Electrium-Mobility/Bakfiets-F26/docs/images/cad-previews/3_hole_connecting_part.png

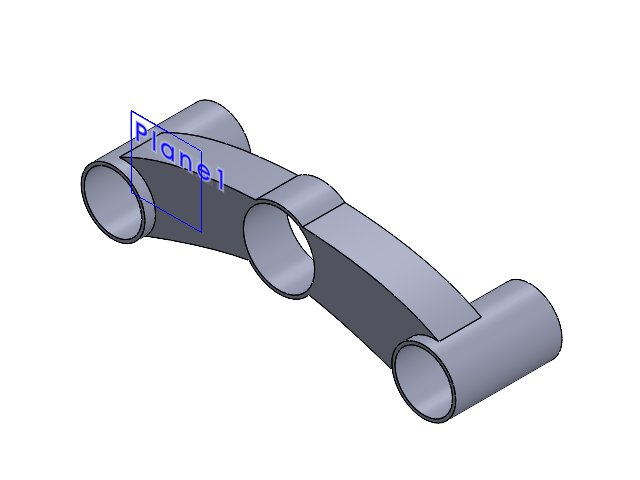
docs/images/cad-previews/3_hole_connecting_part.png
