Electrium-Mobility/Bakfiets-F26/docs/images/cad-previews/91280A626_Medium_Strength_Class_8_8_Steel_Hex_Head_Screw.png

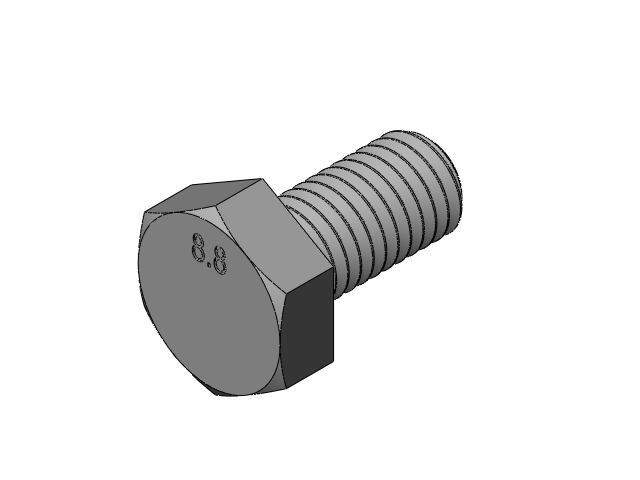
docs/images/cad-previews/91280A626_Medium_Strength_Class_8_8_Steel_Hex_Head_Screw.png
