Electrium-Mobility/Bakfiets-F26/docs/images/cad-previews/Aluminum_Angle_1_25_x_0_125_.png

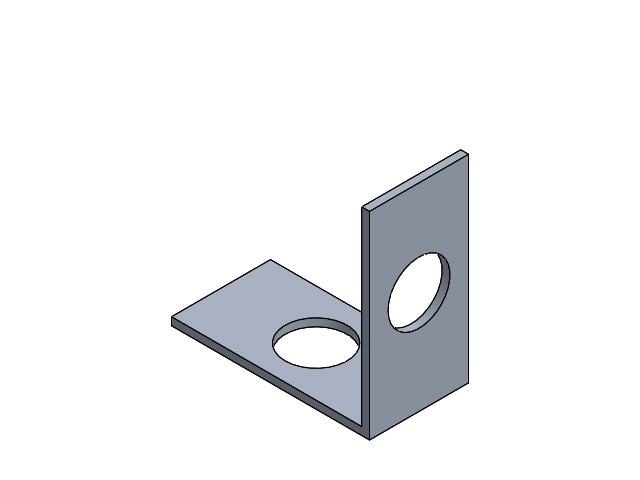
docs/images/cad-previews/Aluminum_Angle_1_25_x_0_125_.png
