Electrium-Mobility/Bakfiets-F26/docs/images/cad-previews/Antispark.png

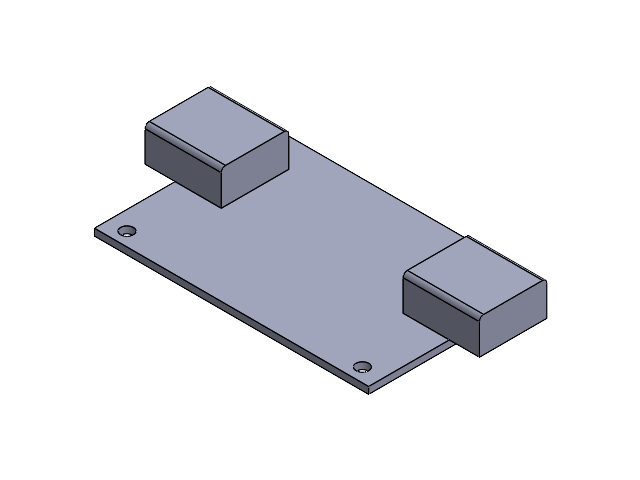
docs/images/cad-previews/Antispark.png
