Electrium-Mobility/Bakfiets-F26/docs/images/cad-previews/Assem1.png

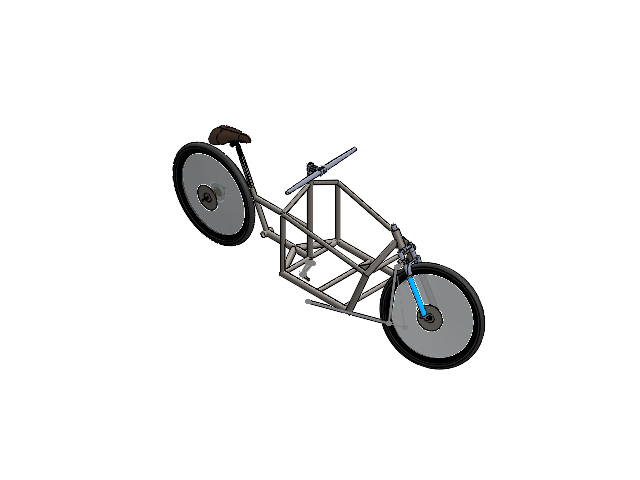
docs/images/cad-previews/Assem1.png
