Electrium-Mobility/Bakfiets-F26/docs/images/cad-previews/bakfiets_front_fork.png

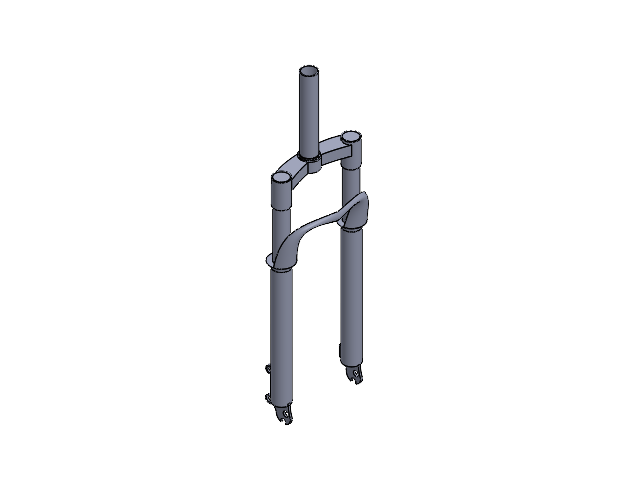
docs/images/cad-previews/bakfiets_front_fork.png
