Electrium-Mobility/Bakfiets-F26/docs/images/cad-previews/ball.png

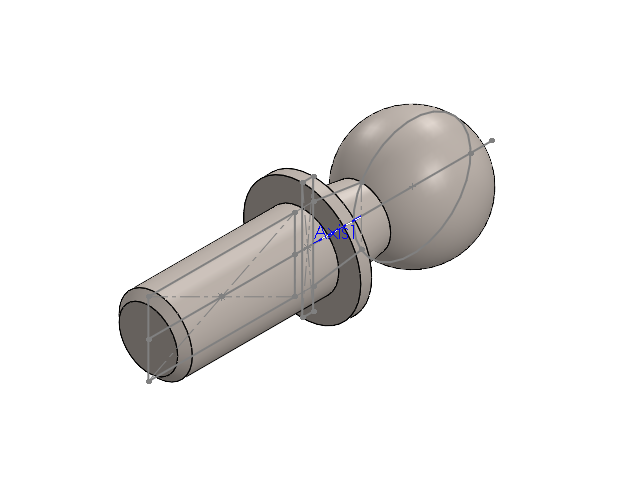
docs/images/cad-previews/ball.png
