Electrium-Mobility/Bakfiets-F26/docs/images/cad-previews/ball_joint.png

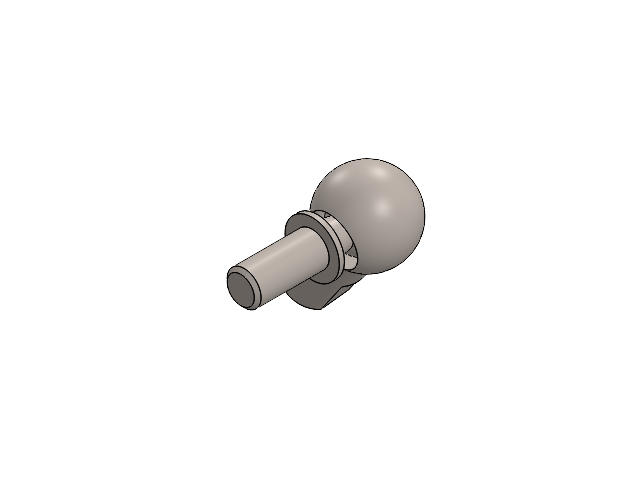
docs/images/cad-previews/ball_joint.png
