Electrium-Mobility/Bakfiets-F26/docs/images/cad-previews/BottomBracketClamp.png

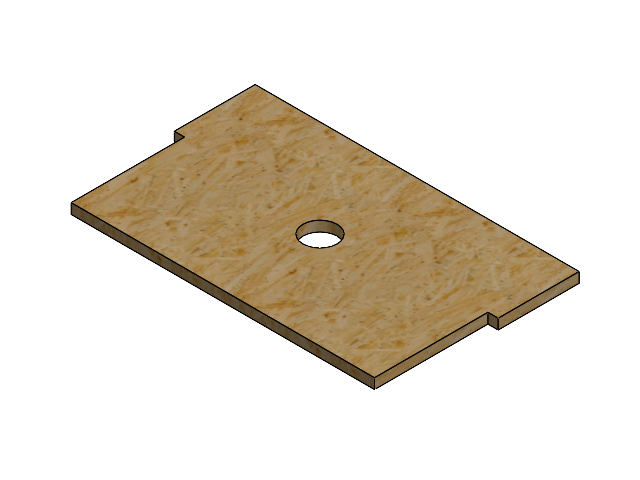
docs/images/cad-previews/BottomBracketClamp.png
