Electrium-Mobility/Bakfiets-F26/docs/images/cad-previews/BottomBracketSupport.png

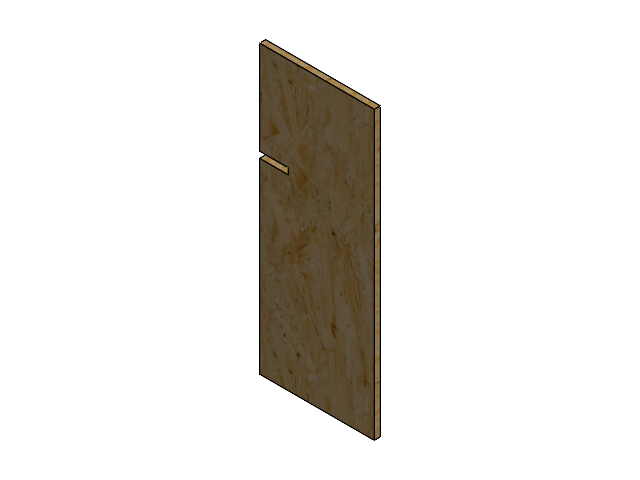
docs/images/cad-previews/BottomBracketSupport.png
