Electrium-Mobility/Bakfiets-F26/docs/images/cad-previews/Box_and_Frame.png

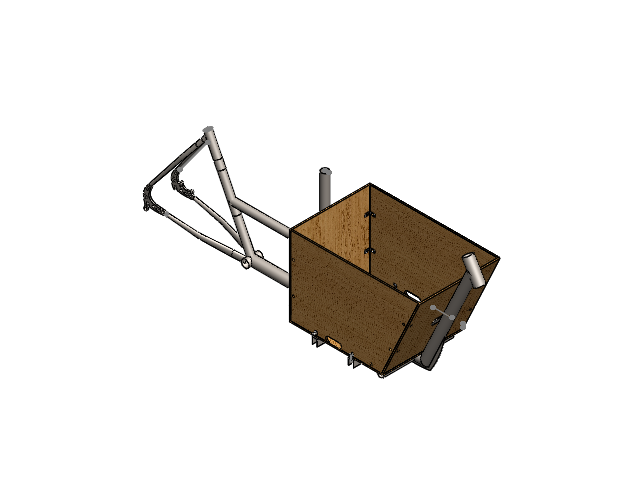
docs/images/cad-previews/Box_and_Frame.png
