Electrium-Mobility/Bakfiets-F26/docs/images/cad-previews/Box_with_angles.png

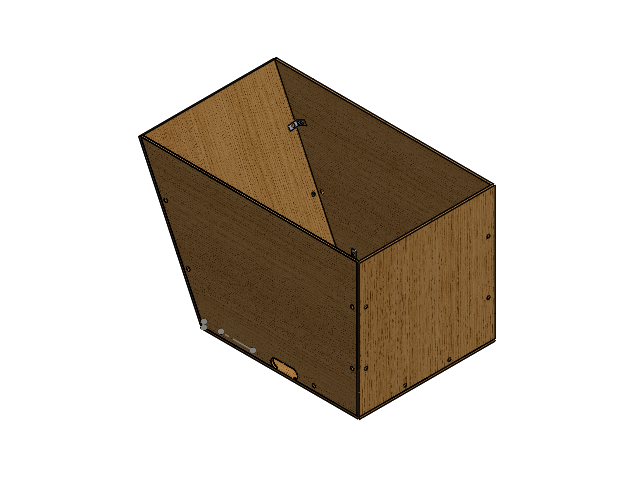
docs/images/cad-previews/Box_with_angles.png
