Electrium-Mobility/Bakfiets-F26/docs/images/cad-previews/Cargo_Box.png

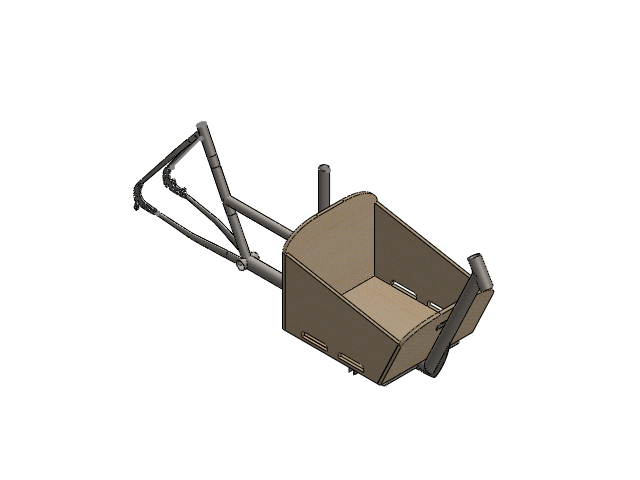
docs/images/cad-previews/Cargo_Box.png
