Electrium-Mobility/Bakfiets-F26/docs/images/cad-previews/Cargo_Box_2.png

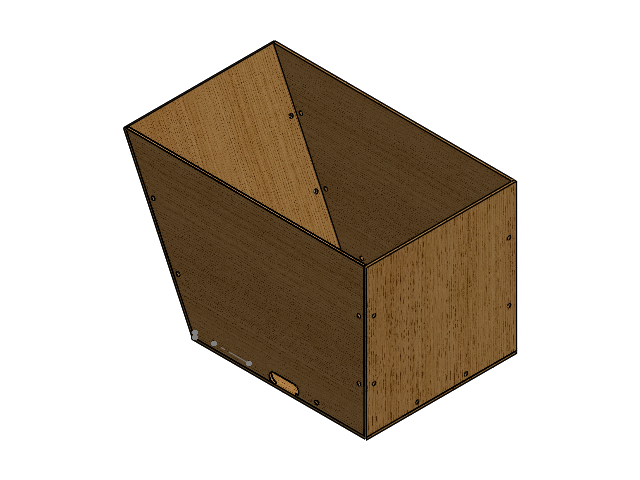
docs/images/cad-previews/Cargo_Box_2.png
