Electrium-Mobility/Bakfiets-F26/docs/images/cad-previews/ChainStaySupport1.png

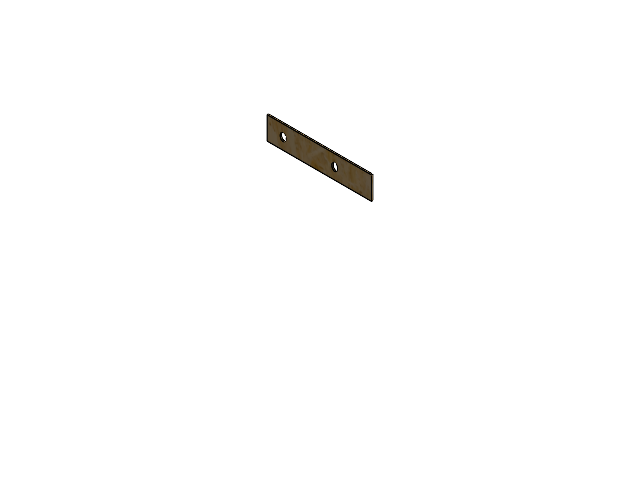
docs/images/cad-previews/ChainStaySupport1.png
