Electrium-Mobility/Bakfiets-F26/docs/images/cad-previews/ChainStaySupport2.png

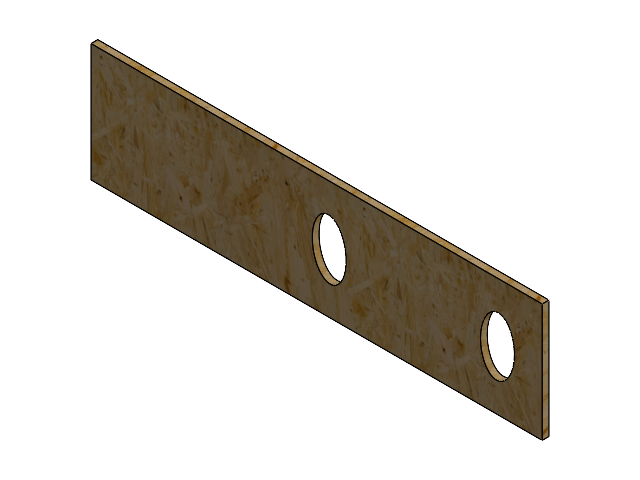
docs/images/cad-previews/ChainStaySupport2.png
