Electrium-Mobility/Bakfiets-F26/docs/images/cad-previews/clamp.png

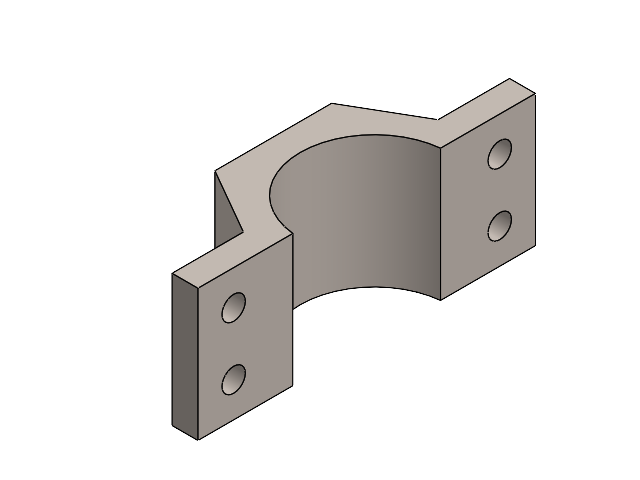
docs/images/cad-previews/clamp.png
