Electrium-Mobility/Bakfiets-F26/docs/images/cad-previews/ConeSupportConnector.png

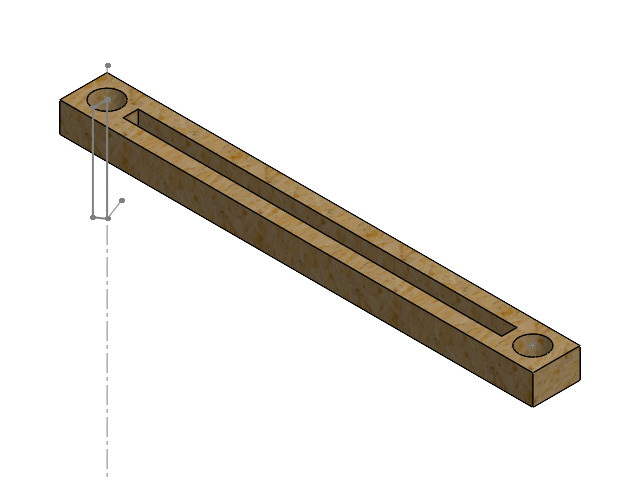
docs/images/cad-previews/ConeSupportConnector.png
