Electrium-Mobility/Bakfiets-F26/docs/images/cad-previews/coop_bakfiets_ball_joint.png

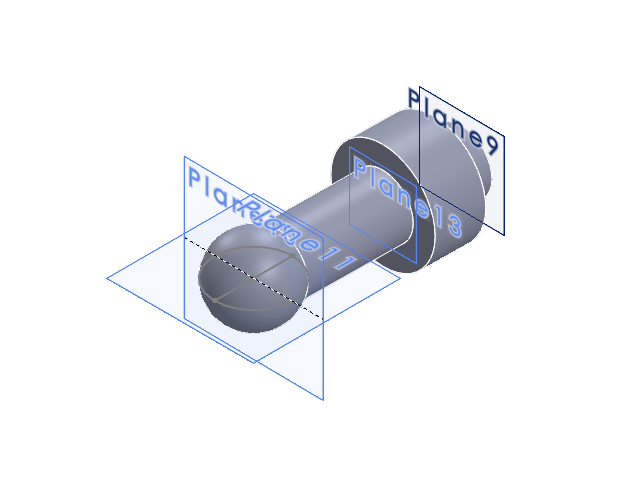
docs/images/cad-previews/coop_bakfiets_ball_joint.png
