Electrium-Mobility/Bakfiets-F26/docs/images/cad-previews/coop_bakfiets_cargo_box_low_detail.png

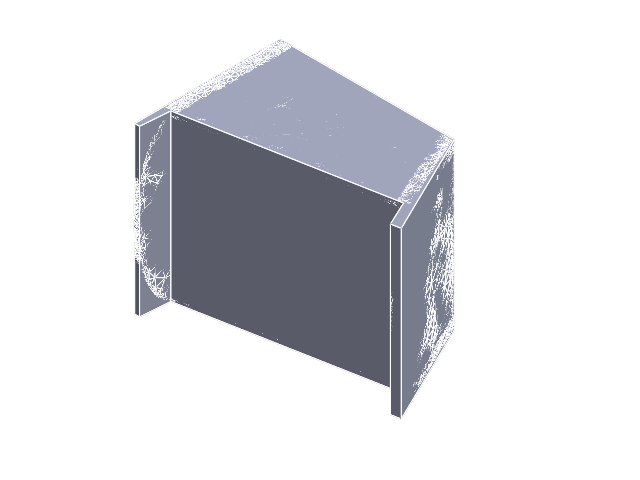
docs/images/cad-previews/coop_bakfiets_cargo_box_low_detail.png
