Electrium-Mobility/Bakfiets-F26/docs/images/cad-previews/coop_bakfiets_frame.png

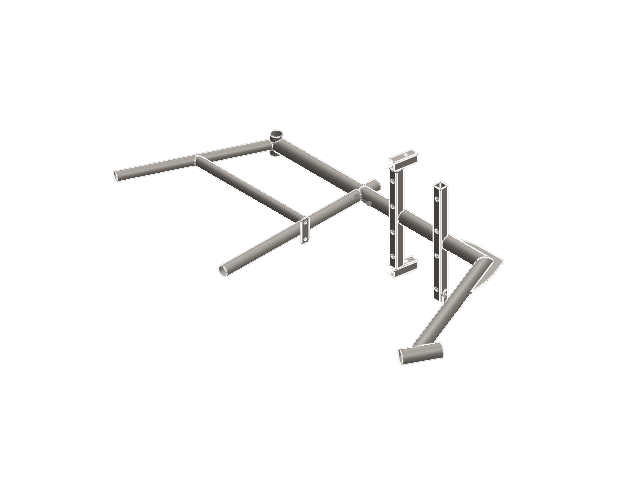
docs/images/cad-previews/coop_bakfiets_frame.png
