Electrium-Mobility/Bakfiets-F26/docs/images/cad-previews/coop_bakfiets_front_suspension.png

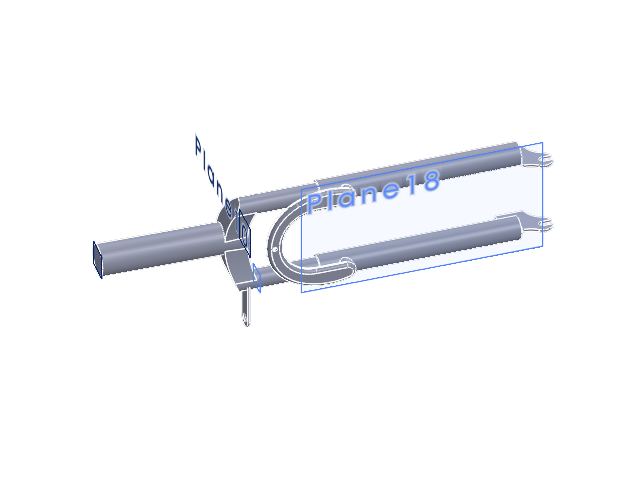
docs/images/cad-previews/coop_bakfiets_front_suspension.png
