Electrium-Mobility/Bakfiets-F26/docs/images/cad-previews/coop_bakfiets_front_wheel.png

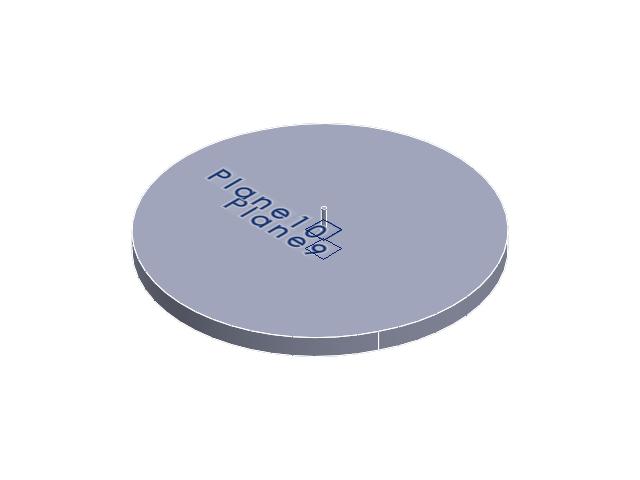
docs/images/cad-previews/coop_bakfiets_front_wheel.png
