Electrium-Mobility/Bakfiets-F26/docs/images/cad-previews/coop_bakfiets_kickstand.png

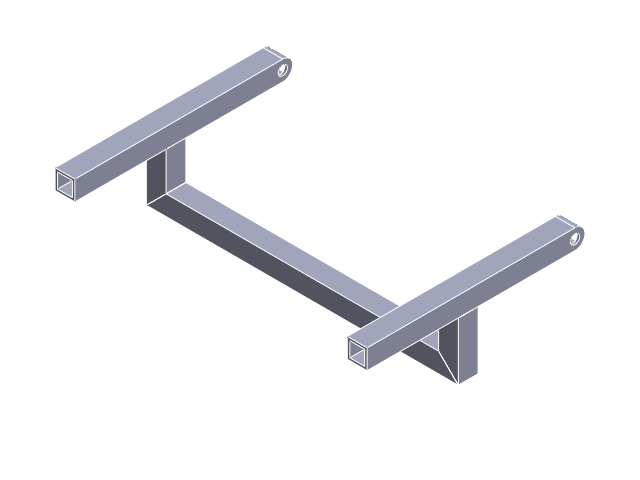
docs/images/cad-previews/coop_bakfiets_kickstand.png
