Electrium-Mobility/Bakfiets-F26/docs/images/cad-previews/coop_bakfiets_main_asm.png

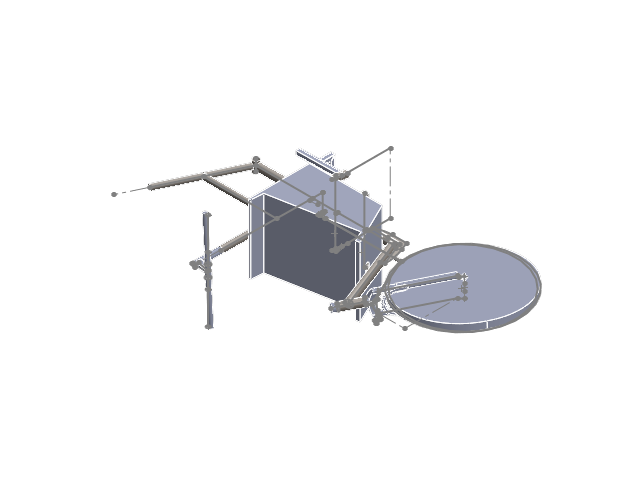
docs/images/cad-previews/coop_bakfiets_main_asm.png
