Electrium-Mobility/Bakfiets-F26/docs/images/cad-previews/coop_bakfiets_master_sketch.png

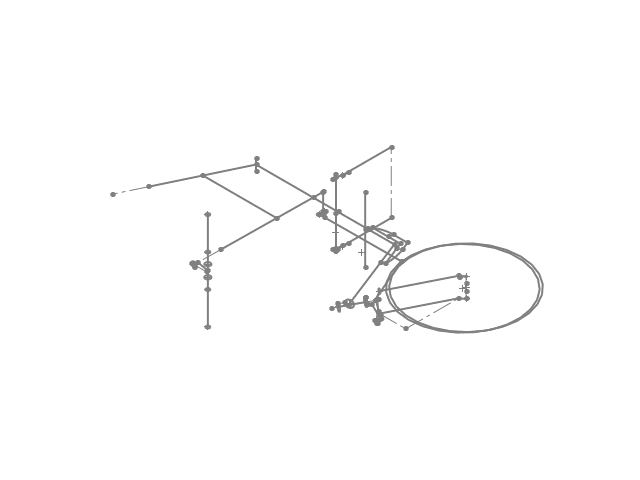
docs/images/cad-previews/coop_bakfiets_master_sketch.png
