Electrium-Mobility/Bakfiets-F26/docs/images/cad-previews/coop_bakfiets_steering_rod.png

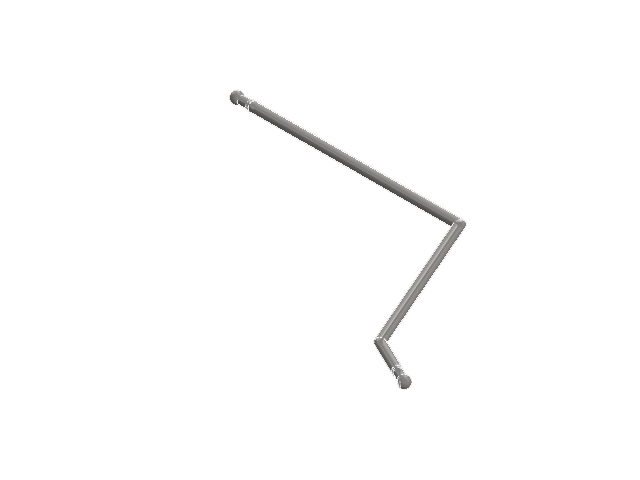
docs/images/cad-previews/coop_bakfiets_steering_rod.png
