Electrium-Mobility/Bakfiets-F26/docs/images/cad-previews/Crank_.png

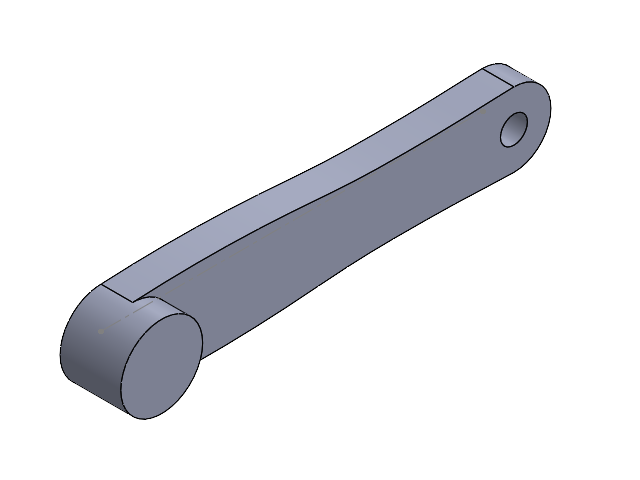
docs/images/cad-previews/Crank_.png
