Electrium-Mobility/Bakfiets-F26/docs/images/cad-previews/Crank_Shaft.png

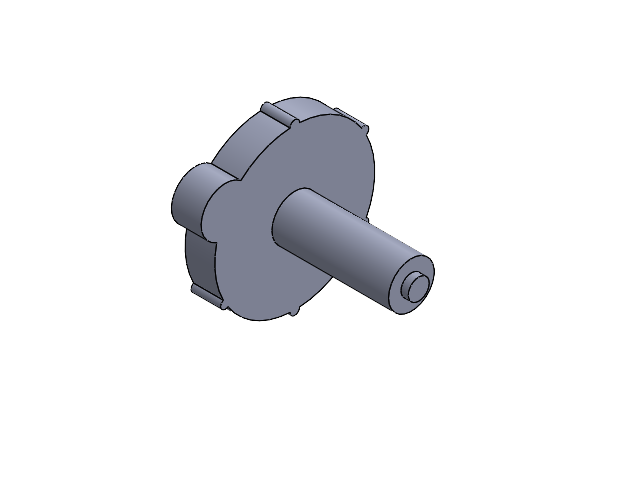
docs/images/cad-previews/Crank_Shaft.png
