Electrium-Mobility/Bakfiets-F26/docs/images/cad-previews/Crank_Wheel.png

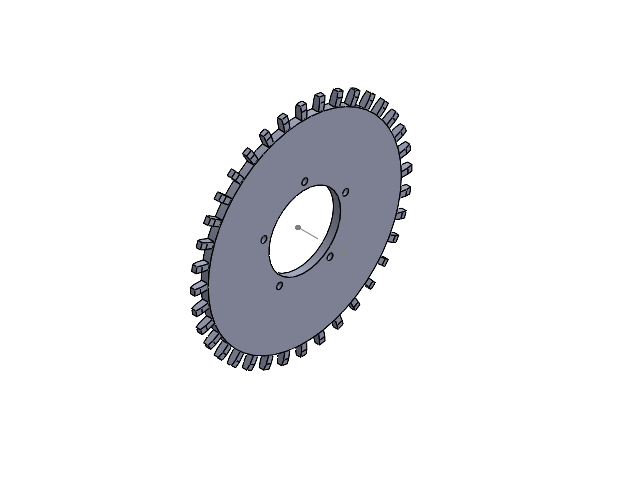
docs/images/cad-previews/Crank_Wheel.png
