Electrium-Mobility/Bakfiets-F26/docs/images/cad-previews/Crank_Wheel_screws.png

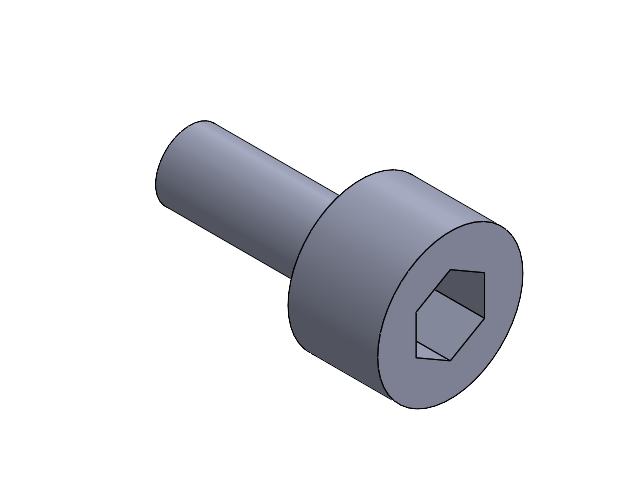
docs/images/cad-previews/Crank_Wheel_screws.png
