Electrium-Mobility/Bakfiets-F26/docs/images/cad-previews/Custom_Angle_for_Sides_3.png

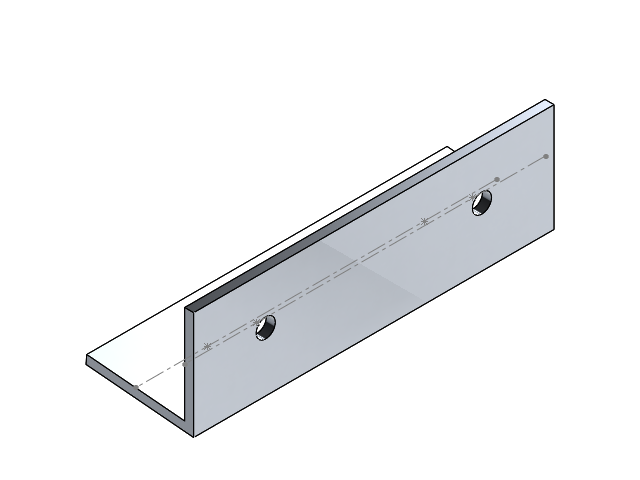
docs/images/cad-previews/Custom_Angle_for_Sides_3.png
