Electrium-Mobility/Bakfiets-F26/docs/images/cad-previews/End1.png

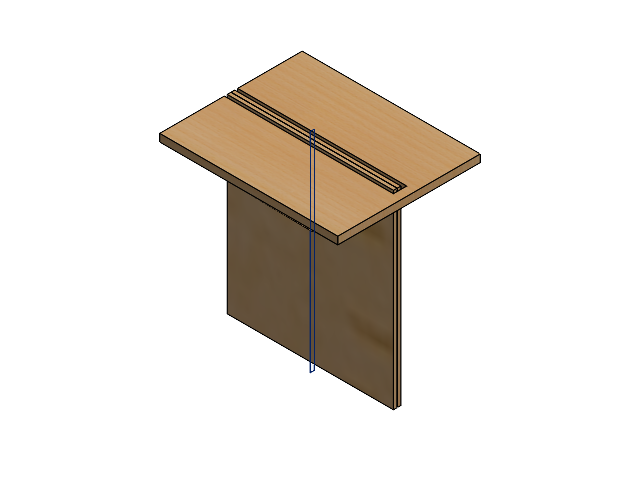
docs/images/cad-previews/End1.png
