Electrium-Mobility/Bakfiets-F26/docs/images/cad-previews/Frame.png

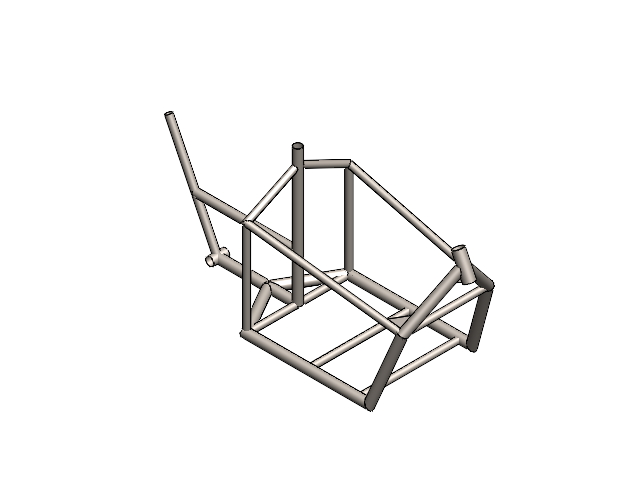
docs/images/cad-previews/Frame.png
