Electrium-Mobility/Bakfiets-F26/docs/images/cad-previews/Frame_2_0.png

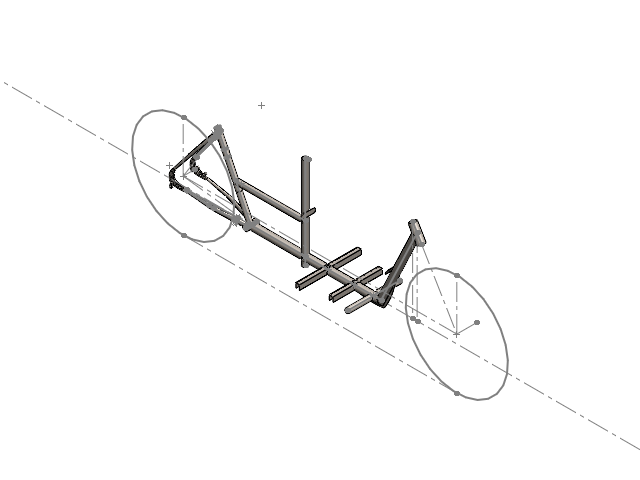
docs/images/cad-previews/Frame_2_0.png
