Electrium-Mobility/Bakfiets-F26/docs/images/cad-previews/Frame_2_0_Sweep8.png

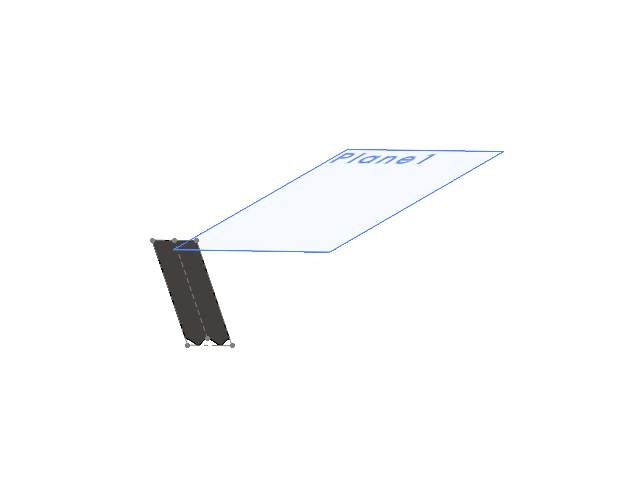
docs/images/cad-previews/Frame_2_0_Sweep8.png
