Electrium-Mobility/Bakfiets-F26/docs/images/cad-previews/front_fork.png

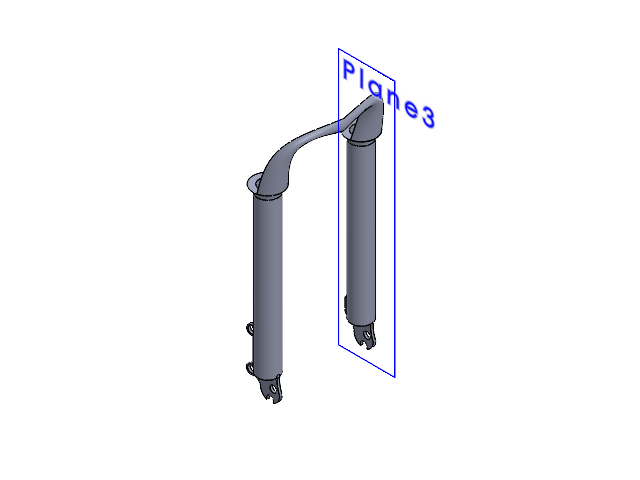
docs/images/cad-previews/front_fork.png
