Electrium-Mobility/Bakfiets-F26/docs/images/cad-previews/front_steering_plate.png

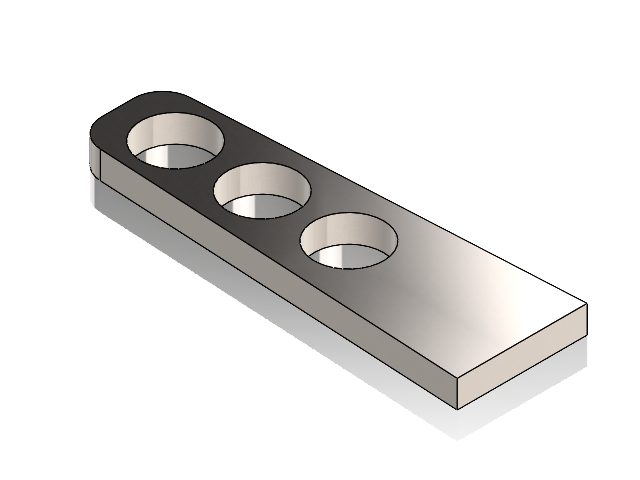
docs/images/cad-previews/front_steering_plate.png
