Electrium-Mobility/Bakfiets-F26/docs/images/cad-previews/front_wheel.png

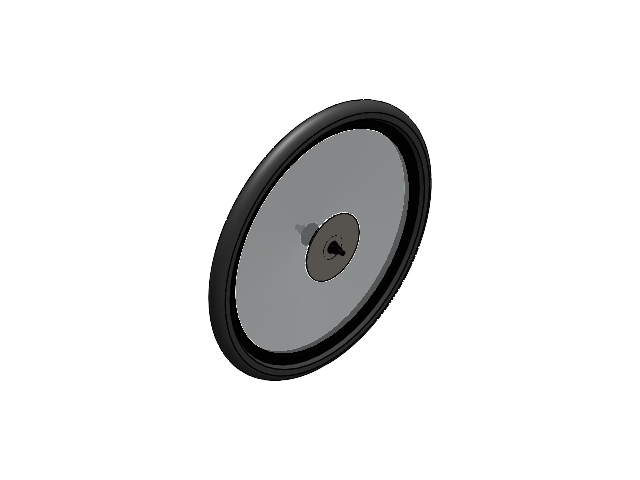
docs/images/cad-previews/front_wheel.png
