Electrium-Mobility/Bakfiets-F26/docs/images/cad-previews/Gusset.png

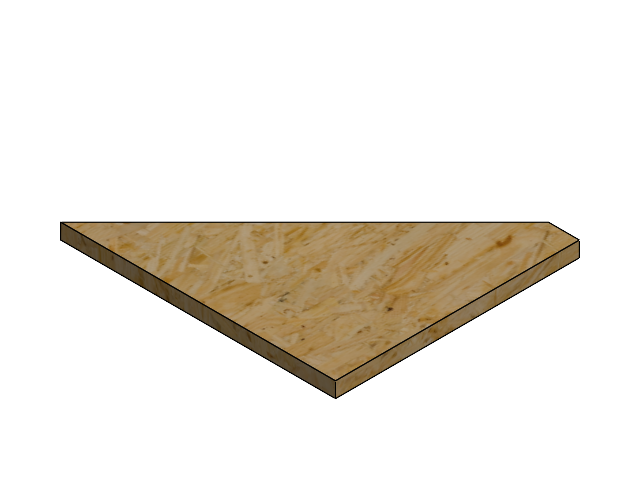
docs/images/cad-previews/Gusset.png
