Electrium-Mobility/Bakfiets-F26/docs/images/cad-previews/handlebar_stem.png

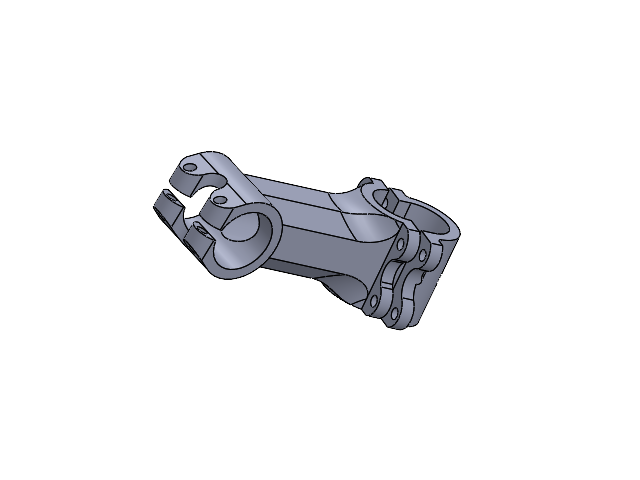
docs/images/cad-previews/handlebar_stem.png
