Electrium-Mobility/Bakfiets-F26/docs/images/cad-previews/handlebars_rod.png

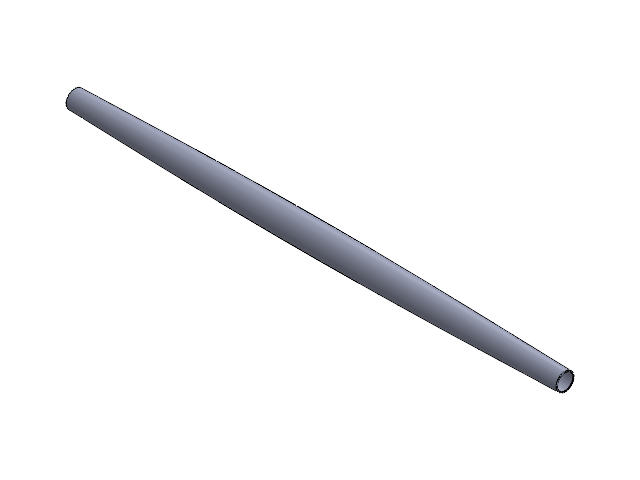
docs/images/cad-previews/handlebars_rod.png
