Electrium-Mobility/Bakfiets-F26/docs/images/cad-previews/JigBaseMDFNew1.png

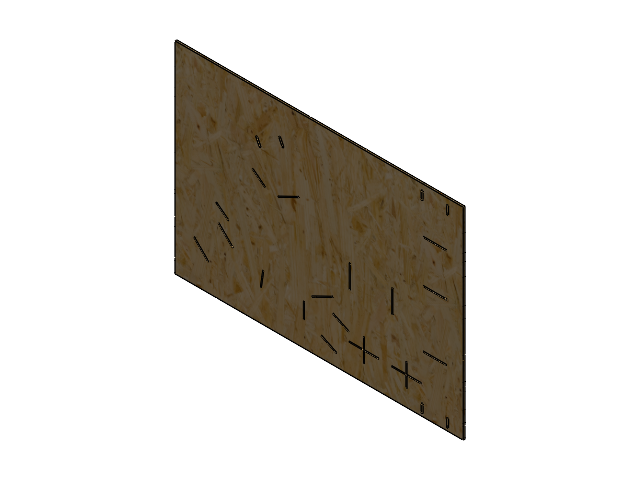
docs/images/cad-previews/JigBaseMDFNew1.png
