Electrium-Mobility/Bakfiets-F26/docs/images/cad-previews/JigCone.png

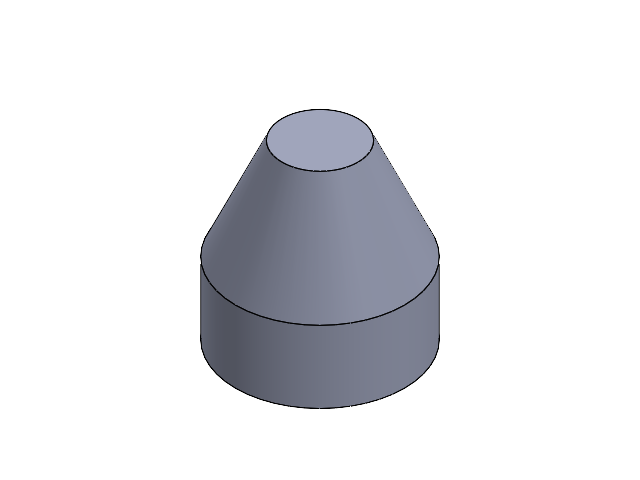
docs/images/cad-previews/JigCone.png
