Electrium-Mobility/Bakfiets-F26/docs/images/cad-previews/JigV2.png

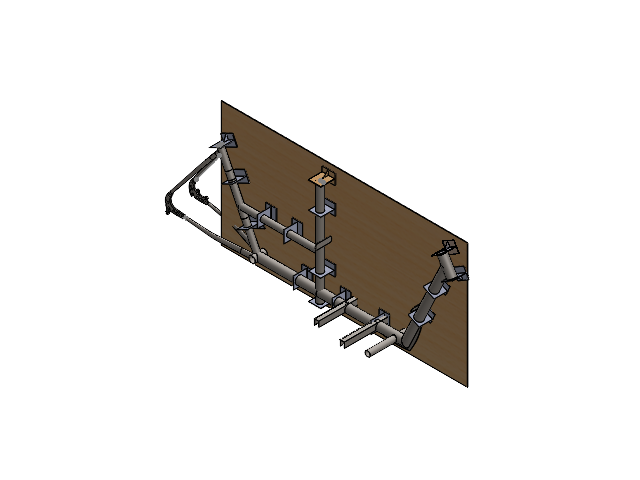
docs/images/cad-previews/JigV2.png
