Electrium-Mobility/Bakfiets-F26/docs/images/cad-previews/Kickstand.png

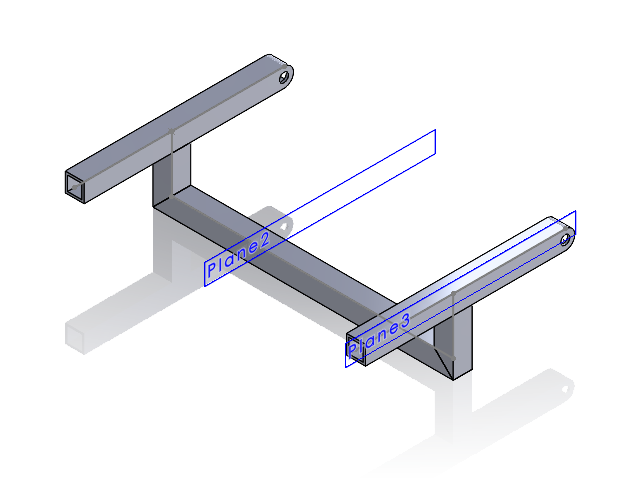
docs/images/cad-previews/Kickstand.png
