Electrium-Mobility/Bakfiets-F26/docs/images/cad-previews/KickstandBracketFeb15.png

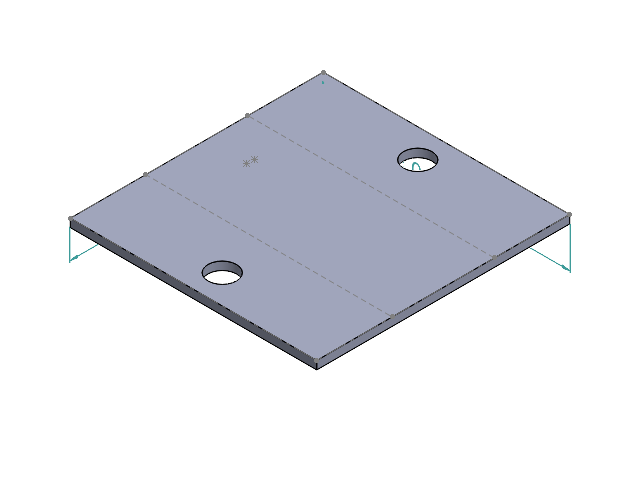
docs/images/cad-previews/KickstandBracketFeb15.png
