Electrium-Mobility/Bakfiets-F26/docs/images/cad-previews/Main_Tube_to_BB.png

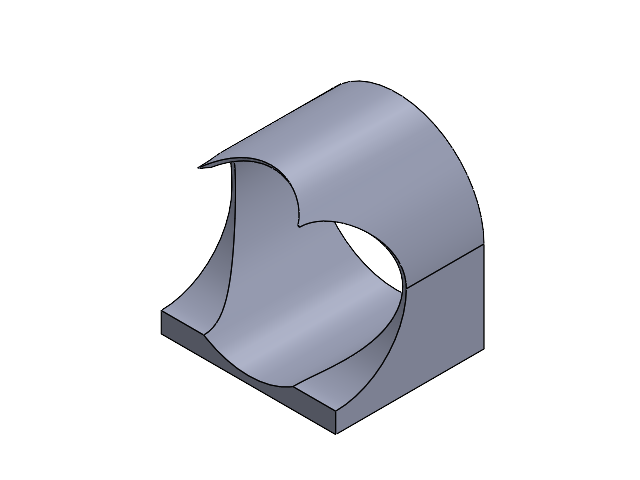
docs/images/cad-previews/Main_Tube_to_BB.png
