Electrium-Mobility/Bakfiets-F26/docs/images/cad-previews/Main_Tube_to_MTH.png

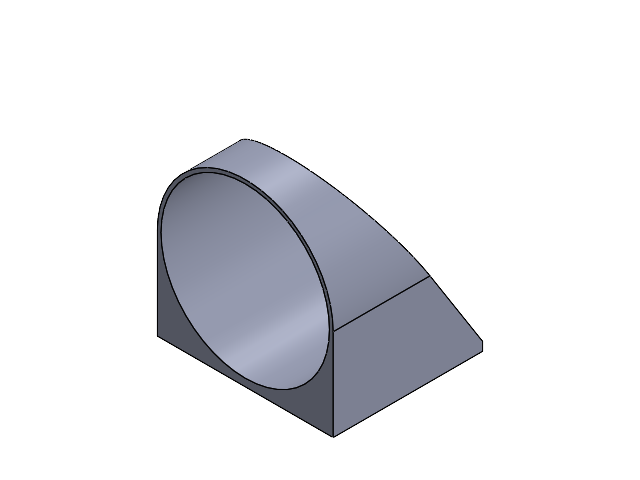
docs/images/cad-previews/Main_Tube_to_MTH.png
