Electrium-Mobility/Bakfiets-F26/docs/images/cad-previews/Motor.png

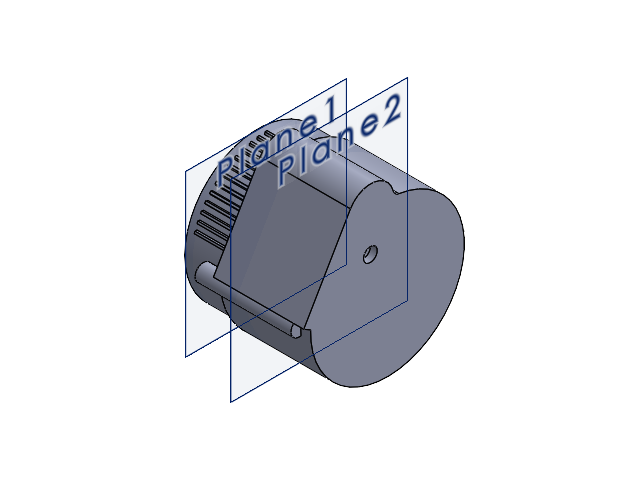
docs/images/cad-previews/Motor.png
