Electrium-Mobility/Bakfiets-F26/docs/images/cad-previews/rear_steering_plate.png

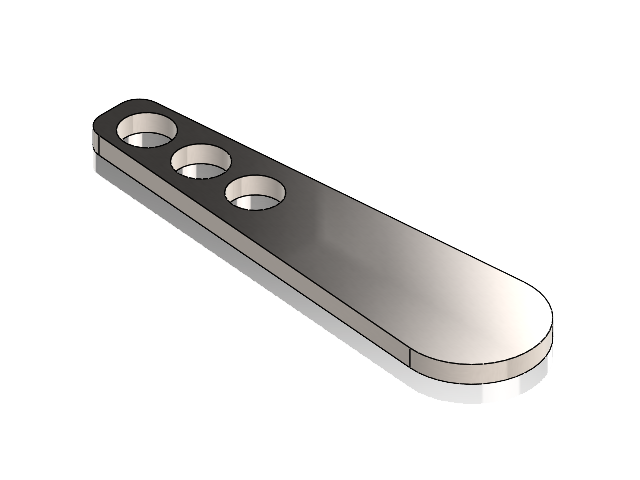
docs/images/cad-previews/rear_steering_plate.png
