Electrium-Mobility/Bakfiets-F26/docs/images/cad-previews/seat.png

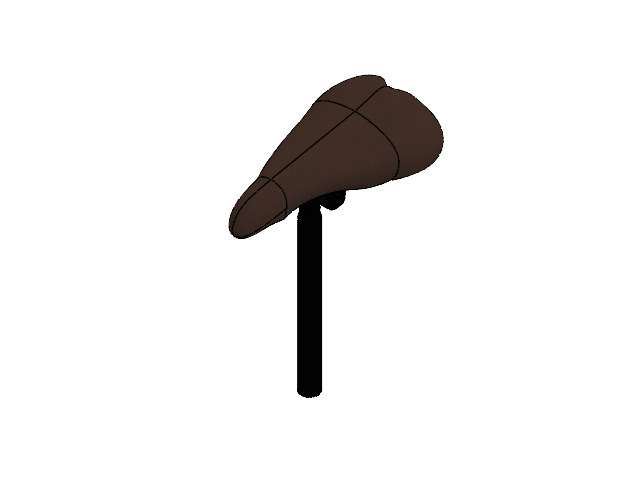
docs/images/cad-previews/seat.png
