Electrium-Mobility/Bakfiets-F26/docs/images/cad-previews/Seat_tube_430_mm_.png

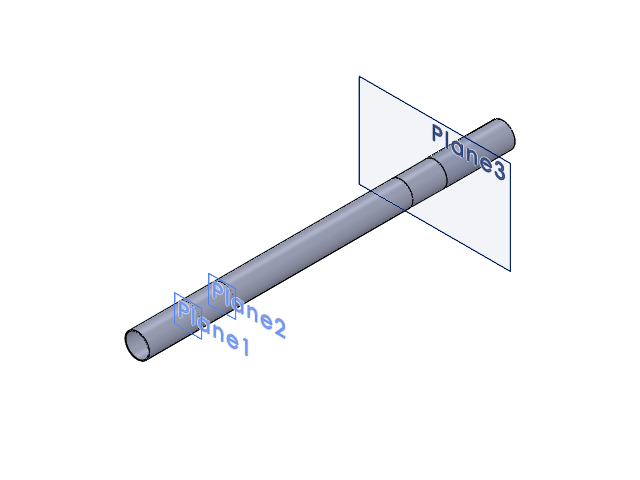
docs/images/cad-previews/Seat_tube_430_mm_.png
