Electrium-Mobility/Bakfiets-F26/docs/images/cad-previews/steering_shaft.png

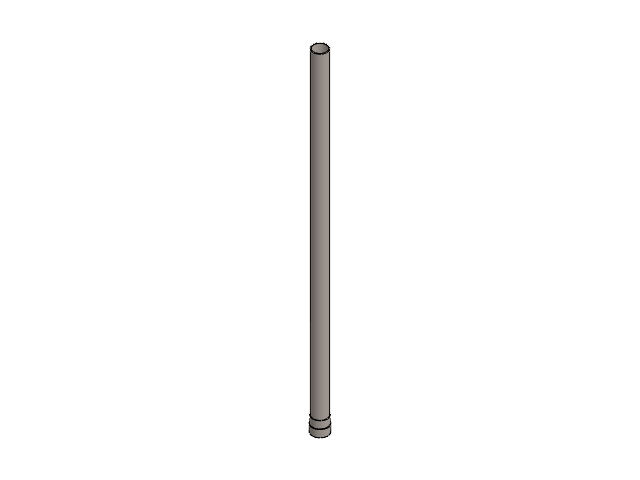
docs/images/cad-previews/steering_shaft.png
