Electrium-Mobility/Bakfiets-F26/docs/images/cad-previews/steeringLink.png

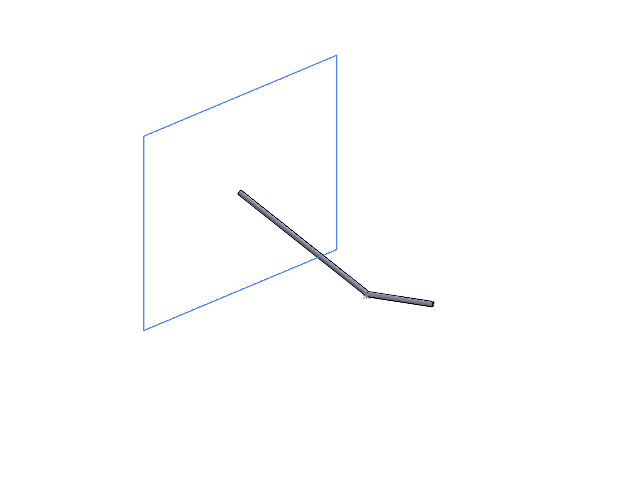
docs/images/cad-previews/steeringLink.png
