Electrium-Mobility/Bakfiets-F26/docs/images/cad-previews/steeringLink_Split1.png

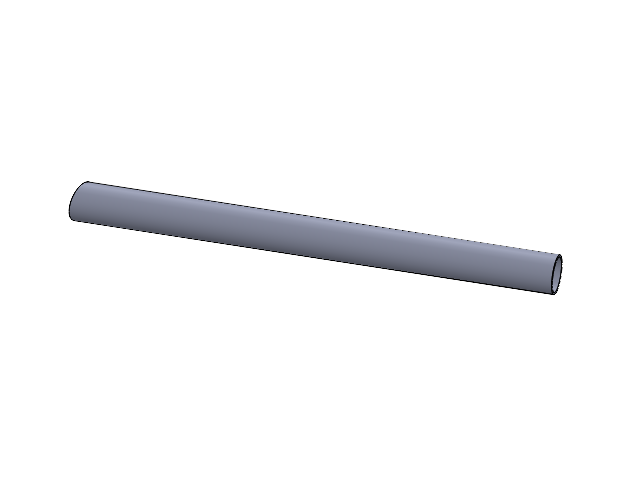
docs/images/cad-previews/steeringLink_Split1.png
