Electrium-Mobility/Bakfiets-F26/docs/images/cad-previews/stem.png

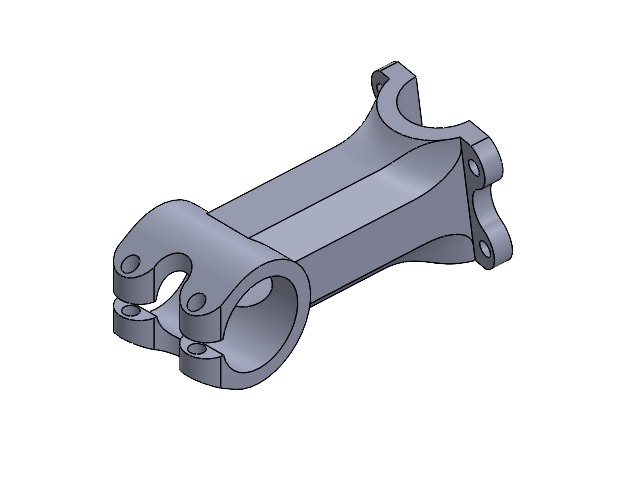
docs/images/cad-previews/stem.png
