Electrium-Mobility/Bakfiets-F26/docs/images/cad-previews/top_stem.png

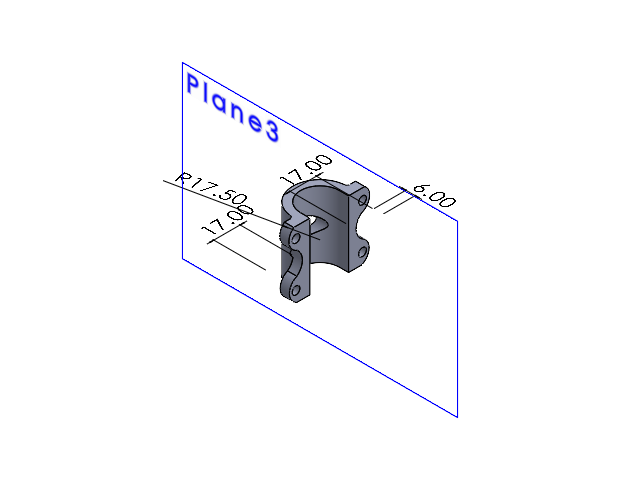
docs/images/cad-previews/top_stem.png
