Electrium-Mobility/Bakfiets-F26/docs/images/cad-previews/Top_tube_460mm_.png

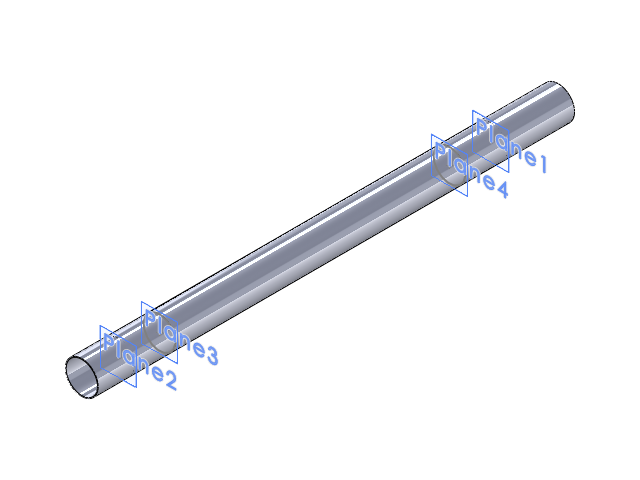
docs/images/cad-previews/Top_tube_460mm_.png
