Electrium-Mobility/Bakfiets-F26/docs/images/cad-previews/turnSignalCase.png

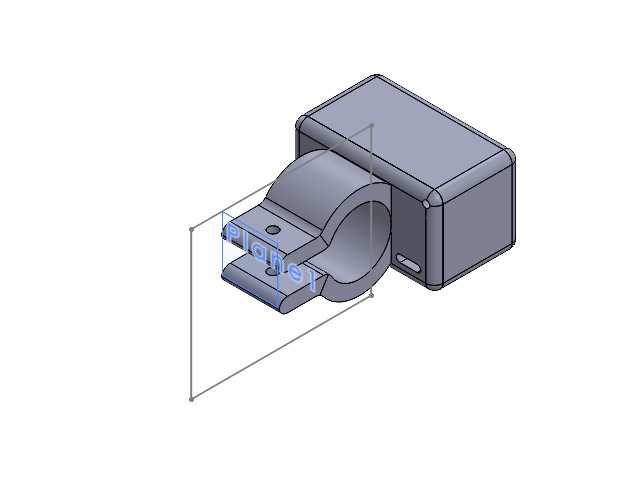
docs/images/cad-previews/turnSignalCase.png
