Electrium-Mobility/Bakfiets-F26/docs/photos/bay-2026-10/antispark.jpg

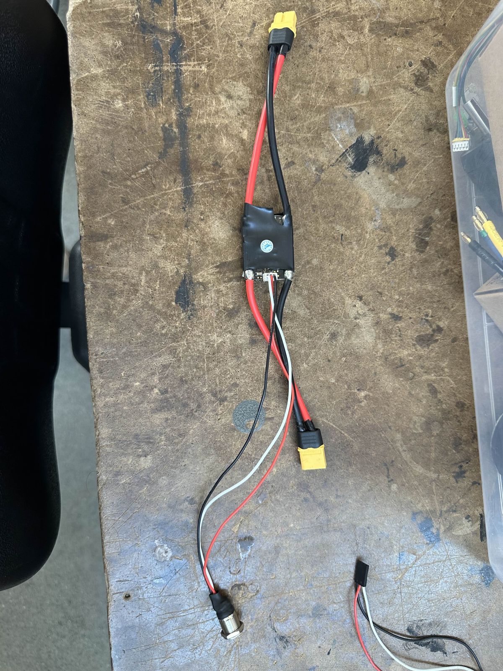
docs/photos/bay-2026-10/antispark.jpg
