Electrium-Mobility/Bakfiets-F26/docs/photos/bay-2026-10/esp32-s3-devkitc-1-box.jpg

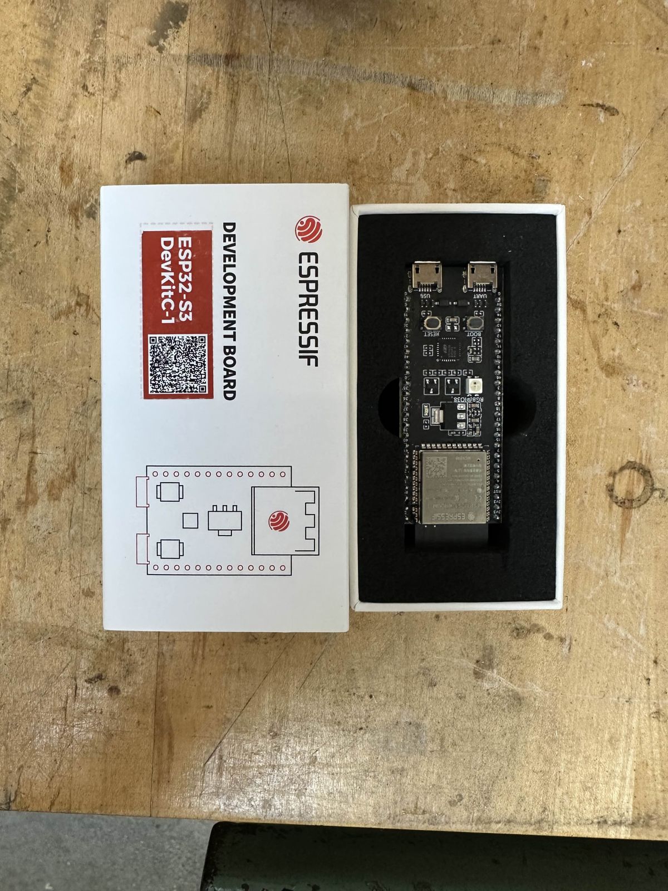
docs/photos/bay-2026-10/esp32-s3-devkitc-1-box.jpg
