Electrium-Mobility/Bakfiets-F26/docs/photos/bay-2026-10/hub-motor-axle-label.jpg

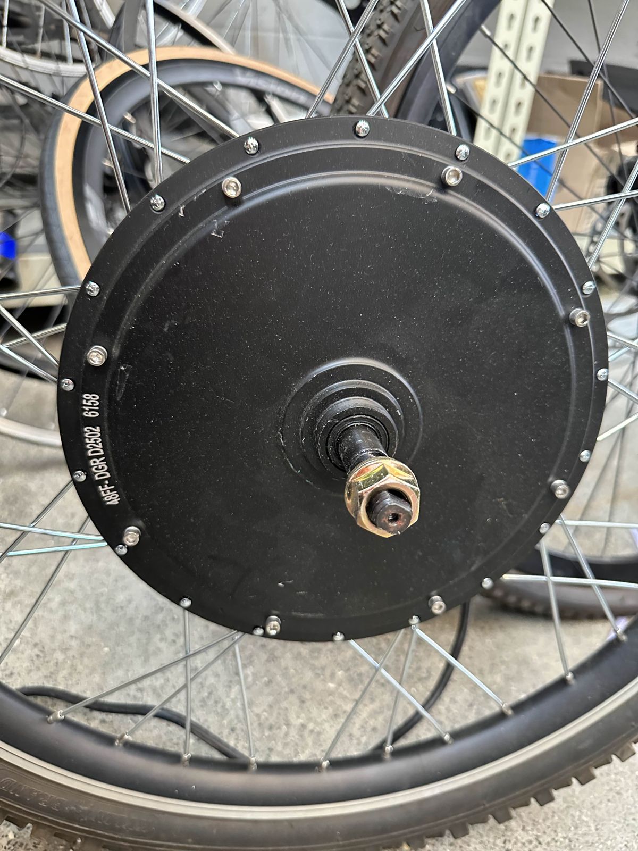
docs/photos/bay-2026-10/hub-motor-axle-label.jpg
