Electrium-Mobility/Bakfiets-F26/docs/photos/bay-2026-10/hub-motor-hall-plug.jpg

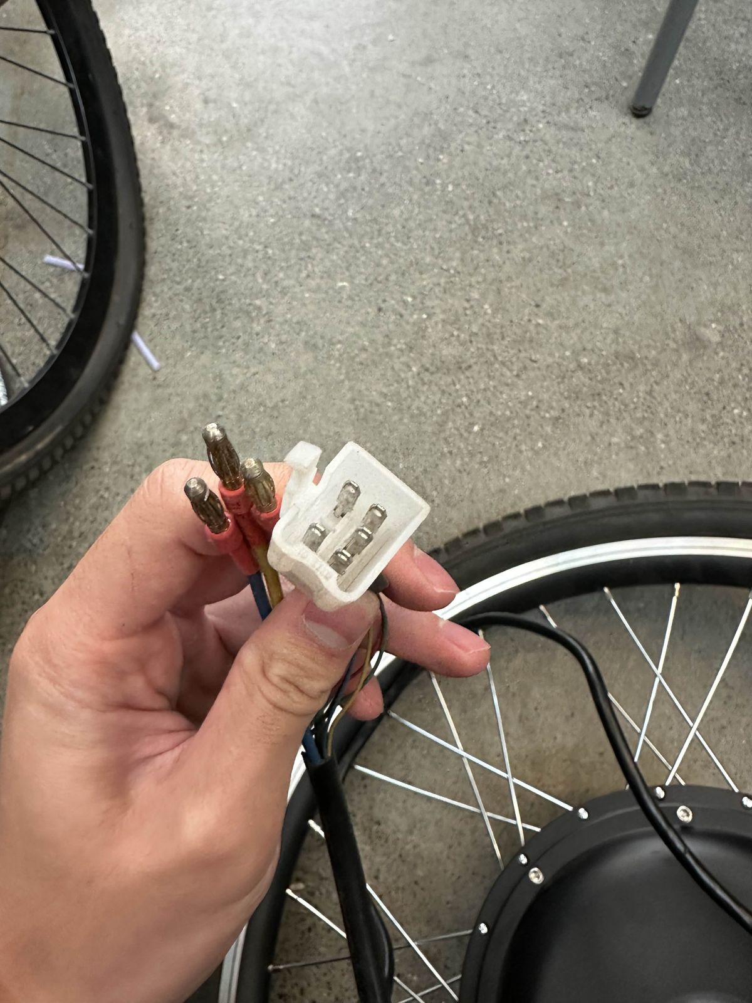
docs/photos/bay-2026-10/hub-motor-hall-plug.jpg
