Electrium-Mobility/Bakfiets-F26/docs/photos/bay-2026-10/hub-motor-phase-and-hall-plugs.jpg

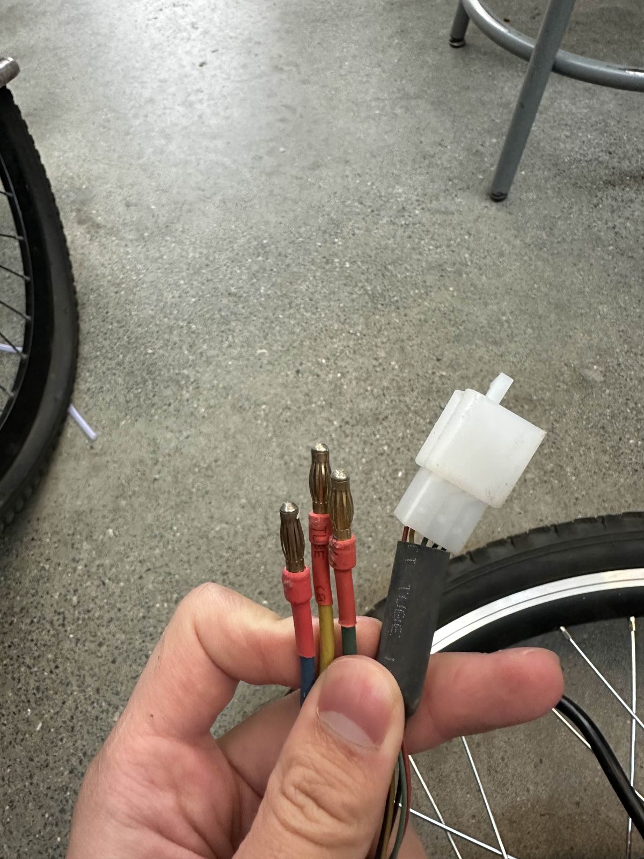
docs/photos/bay-2026-10/hub-motor-phase-and-hall-plugs.jpg
