Electrium-Mobility/Bakfiets-F26/docs/photos/bay-2026-10/motor-controller-heatsink.jpg

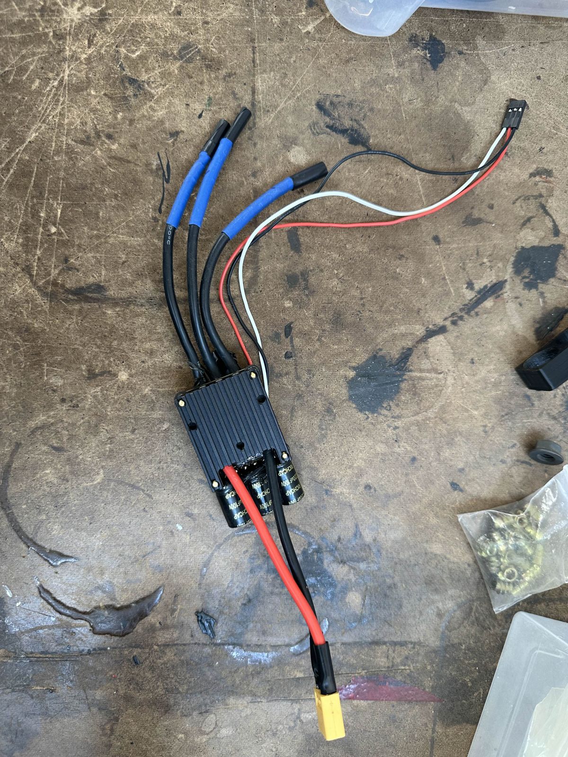
docs/photos/bay-2026-10/motor-controller-heatsink.jpg
