Electrium-Mobility/Bakfiets-F26/docs/photos/bay-2026-10/pack1-label-faded.jpg

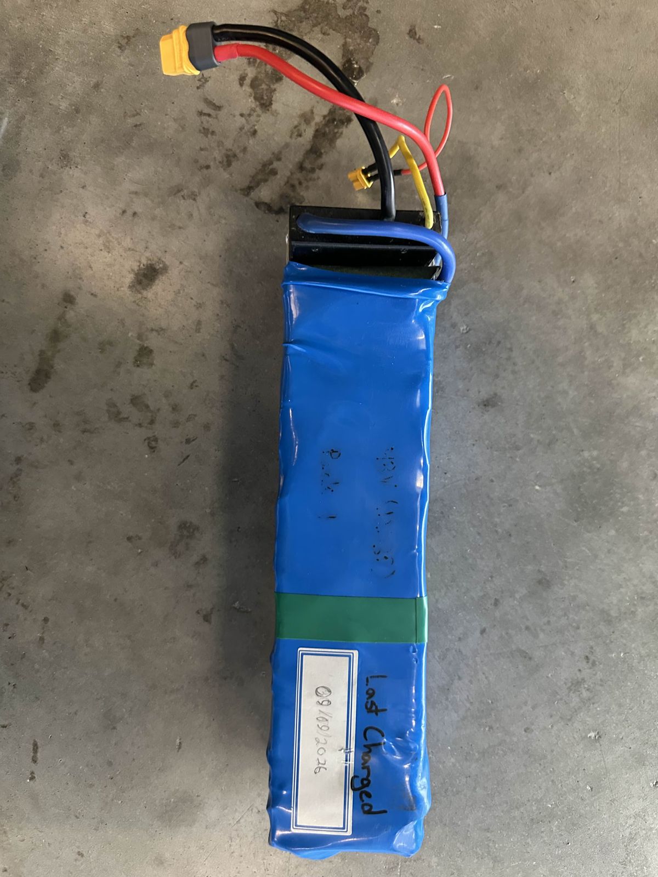
docs/photos/bay-2026-10/pack1-label-faded.jpg
