Electrium-Mobility/Bakfiets-F26/docs/photos/bay-2026-10/pack2-36v-label.jpg

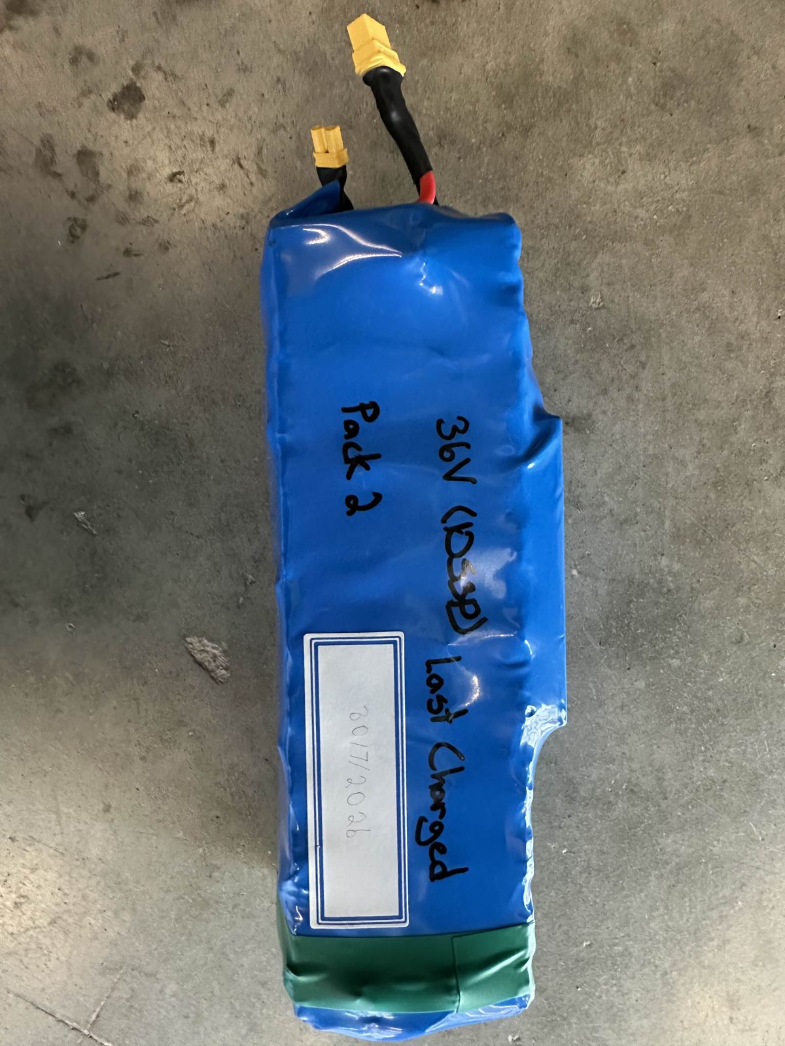
docs/photos/bay-2026-10/pack2-36v-label.jpg
