Electrium-Mobility/Bakfiets-F26/docs/photos/bay-2026-10/pack3-36v-10s2p-label.jpg

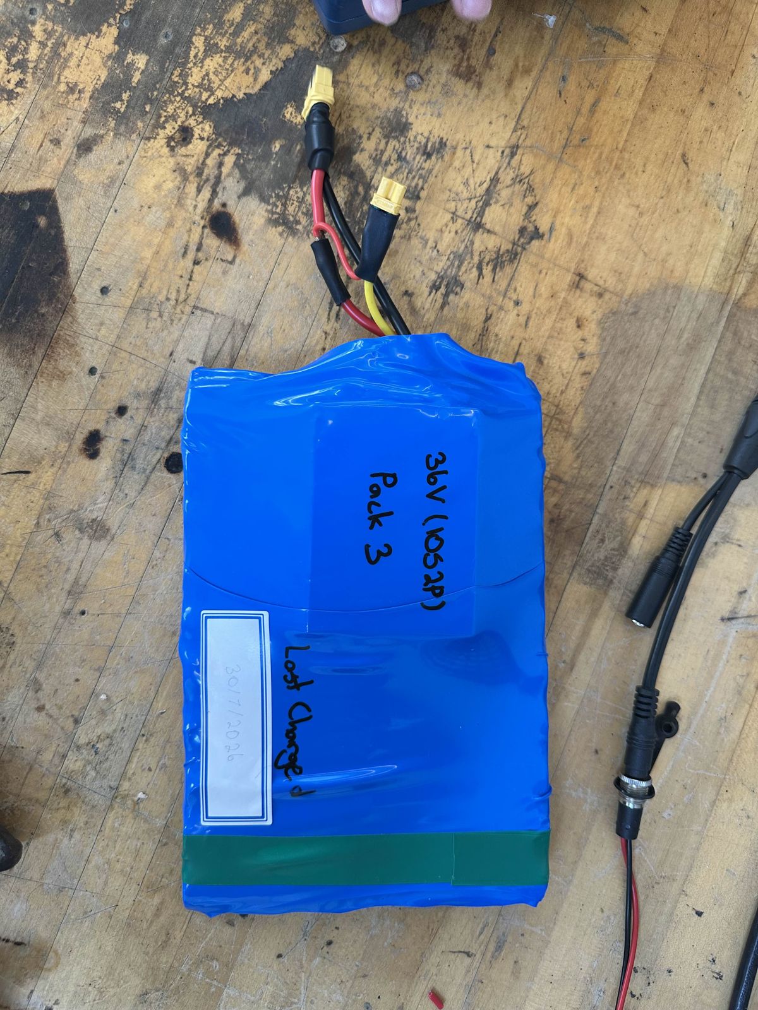
docs/photos/bay-2026-10/pack3-36v-10s2p-label.jpg
