Electrium-Mobility/Bakfiets-F26/docs/photos/bay-2026-10/pack3-connector-and-charge-cable.jpg

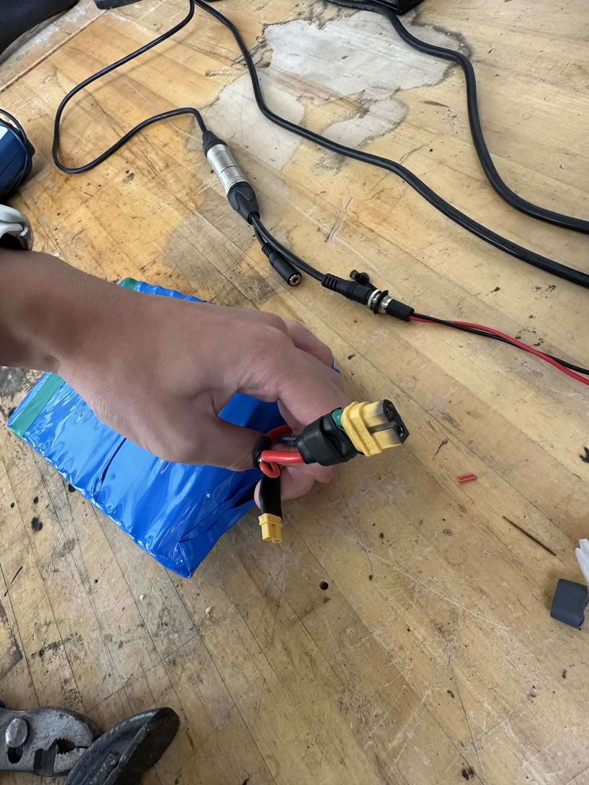
docs/photos/bay-2026-10/pack3-connector-and-charge-cable.jpg
