Electrium-Mobility/Bakfiets-F26/docs/photos/bay-2026-10/spot-welder.jpg

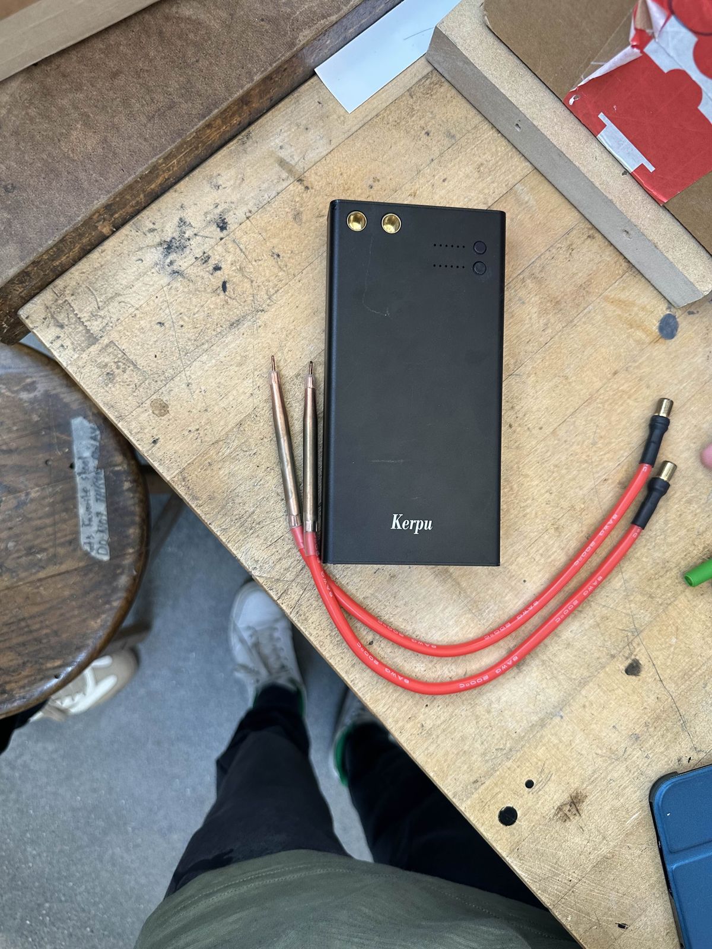
docs/photos/bay-2026-10/spot-welder.jpg
