Electrium-Mobility/Bakfiets-F26/mechanical/cad-2024/Frame 2.0-Sweep8.SLDPRT

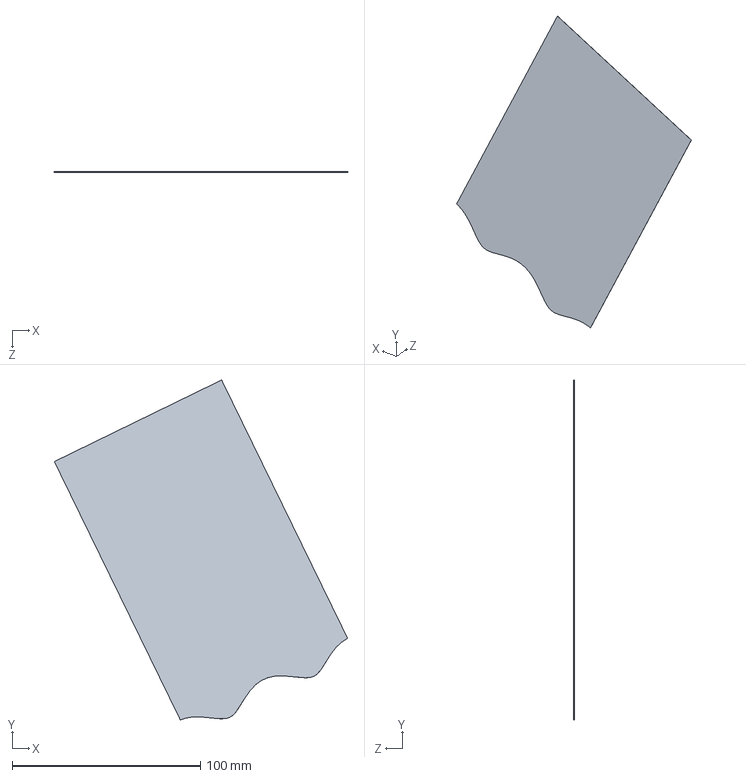
[picture p112: CAD file, 2026-09-26]
mechanical/cad-2024/Frame 2.0-Sweep8.SLDPRT
155.7 x 180.5 x 0.1 mm
