Electrium-Mobility/Bakfiets-F26/mechanical/cad-2024/jig/Jig/BottomBracketClamp.SLDPRT

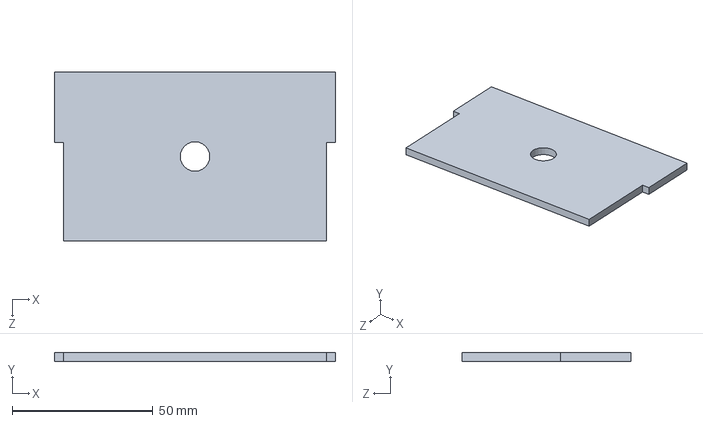
[picture p113: CAD file, 2026-09-26]
mechanical/cad-2024/jig/Jig/BottomBracketClamp.SLDPRT
100.0 x 3.17 x 60.0 mm
