Electrium-Mobility/Bakfiets-F26/mechanical/cad-2024/scrap bike parts/seat.SLDPRT

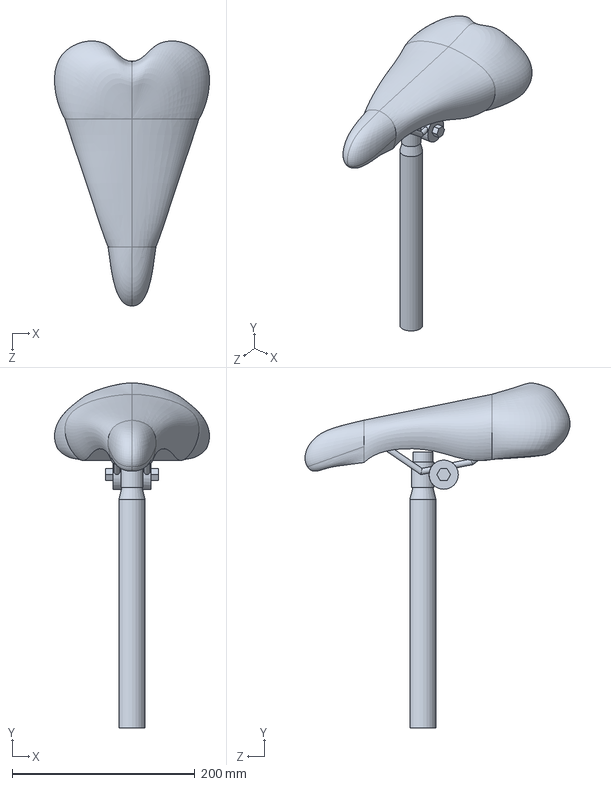
[picture p114: CAD file, 2026-09-26]
mechanical/cad-2024/scrap bike parts/seat.SLDPRT
169.5 x 377.2 x 289.9 mm
