Electrium-Mobility/Bakfiets-F26/mechanical/cad-2024/scrap bike parts/stem parts/turnSignalCaseBottom.STL

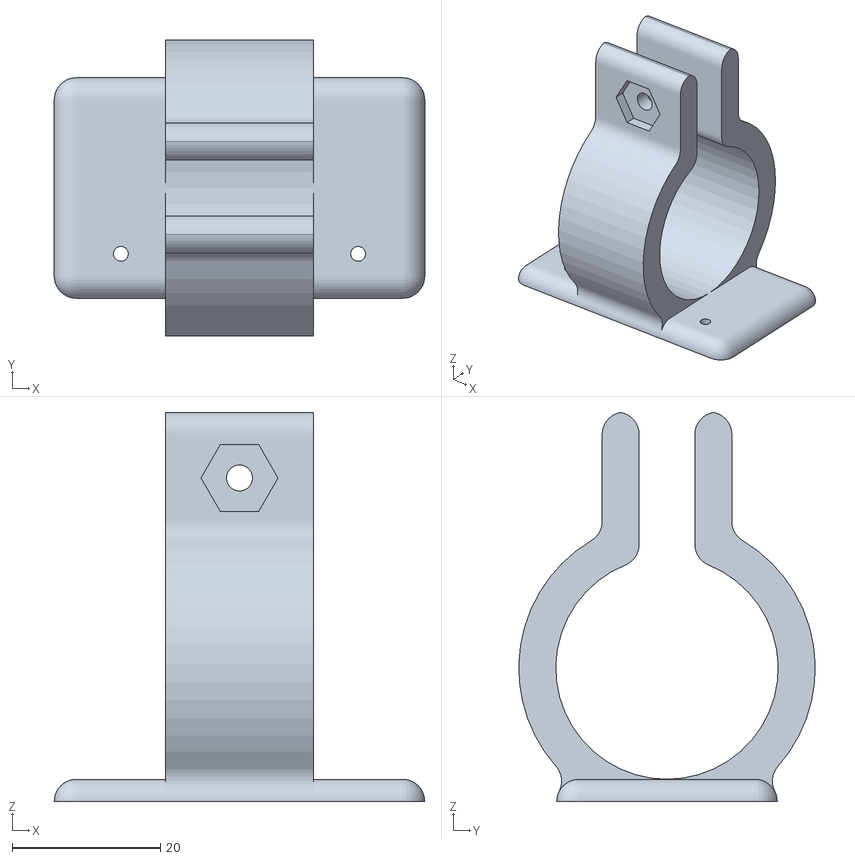
[picture p115: CAD file, 2026-09-26]
mechanical/cad-2024/scrap bike parts/stem parts/turnSignalCaseBottom.STL
50.0 x 40.0 x 52.5
