Electrium-Mobility/Bakfiets-F26/mechanical/cad-2024/Stays/Chain stays.SLDPRT

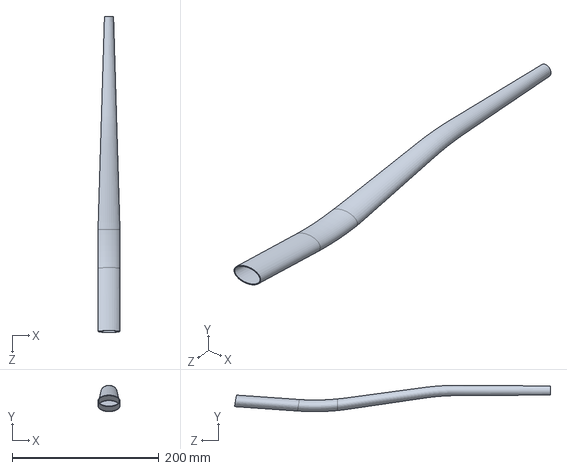
[picture p116: CAD file, 2026-09-26]
mechanical/cad-2024/Stays/Chain stays.SLDPRT
30.0 x 35.9 x 430.7 mm
