Electrium-Mobility/Bakfiets-F26/mechanical/cad-2024/steering system/ball joint/socket.SLDPRT

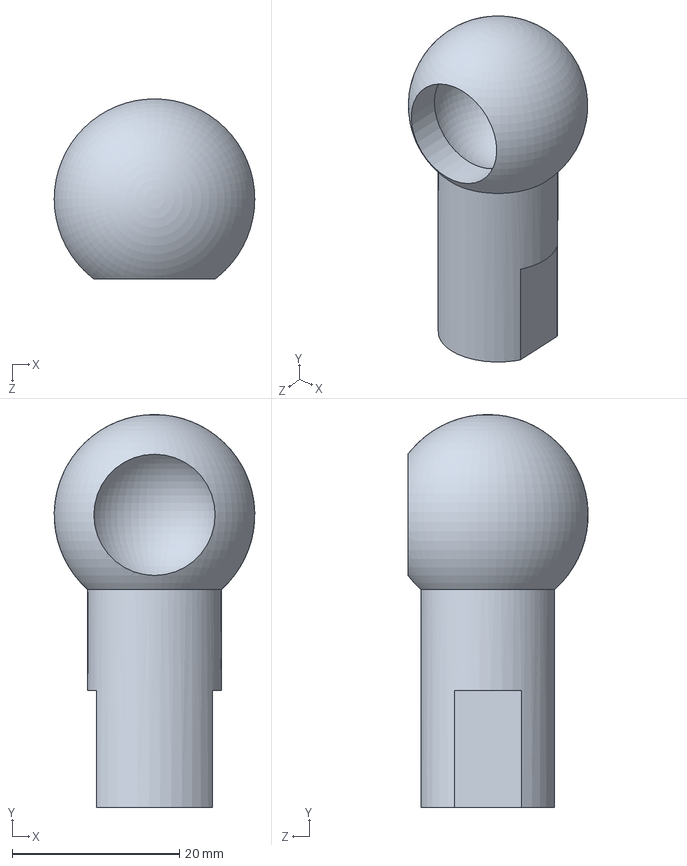
[picture p117: CAD file, 2026-09-26]
mechanical/cad-2024/steering system/ball joint/socket.SLDPRT
24.0 x 47.0 x 21.6 mm
