Electrium-Mobility/Bakfiets-F26/mechanical/cad-2024/steering system/front steering plate.SLDPRT

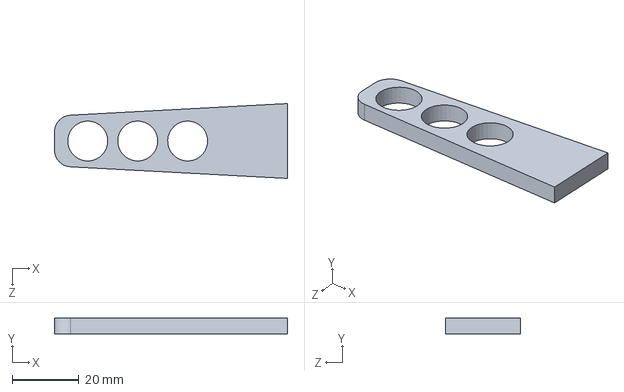
[picture p118: CAD file, 2026-09-26]
mechanical/cad-2024/steering system/front steering plate.SLDPRT
70.0 x 4.76 x 22.5 mm
