Electrium-Mobility/Bakfiets-F26/mechanical/cad-2025-coop/edited-2024-parts/Kickstand.SLDPRT

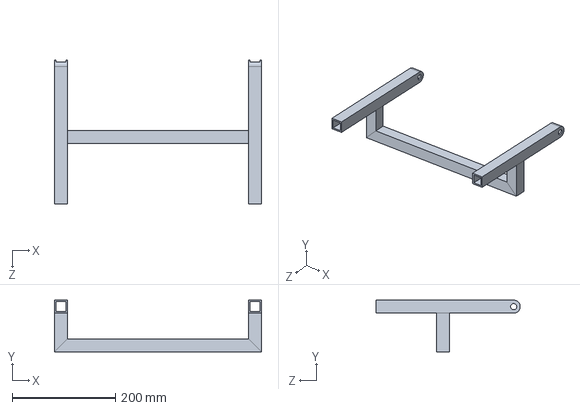
[picture p119: CAD file, 2026-09-26]
mechanical/cad-2025-coop/edited-2024-parts/Kickstand.SLDPRT
401.1 x 100.4 x 280.0 mm
