Electrium-Mobility/Bakfiets-F26/mechanical/cad-2024/battery box/battery pack/Antispark.SLDPRT

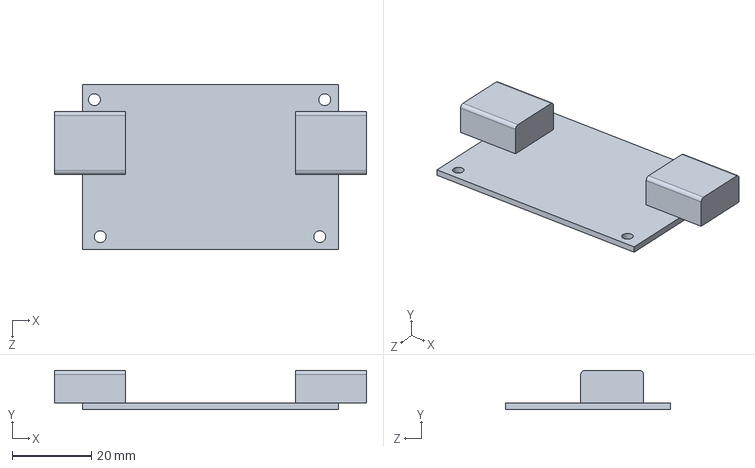
[picture p120: CAD file, 2026-09-26]
mechanical/cad-2024/battery box/battery pack/Antispark.SLDPRT
78.8 x 9.87 x 41.7 mm
