Electrium-Mobility/Bakfiets-F26/mechanical/cad-2024/Frame.SLDPRT

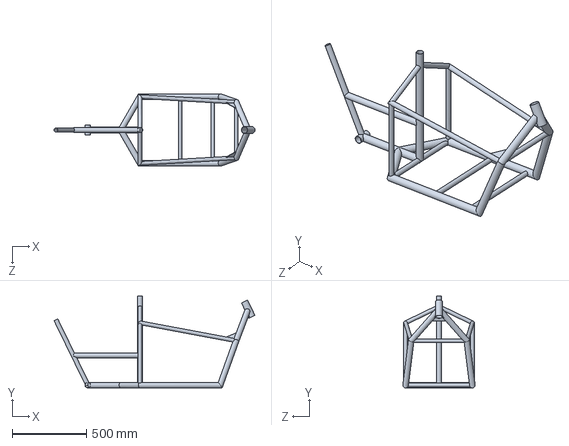
[picture p121: CAD file, 2026-09-26]
mechanical/cad-2024/Frame.SLDPRT
1354.7 x 619.1 x 488.1 mm
