Electrium-Mobility/Bakfiets-F26/mechanical/cad-2024/MotorCrank/Crank Shaft.SLDPRT

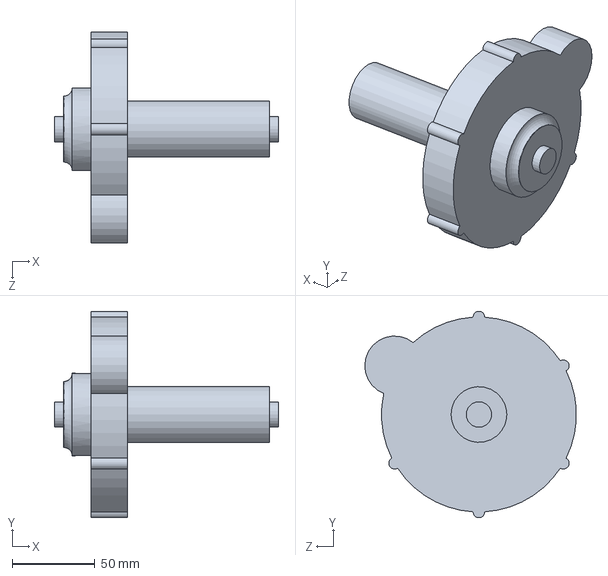
[picture p122: CAD file, 2026-09-26]
mechanical/cad-2024/MotorCrank/Crank Shaft.SLDPRT
135.6 x 124.9 x 128.0 mm
