Electrium-Mobility/Bakfiets-F26/mechanical/cad-2024/scrap bike parts/front fork parts/front fork two rod.SLDPRT

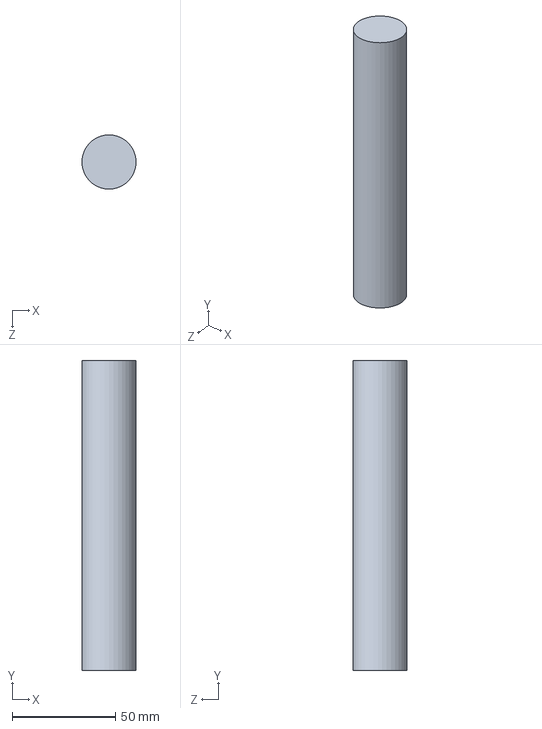
[picture p123: CAD file, 2026-09-26]
mechanical/cad-2024/scrap bike parts/front fork parts/front fork two rod.SLDPRT
26.1 x 150.0 x 26.2 mm
