Electrium-Mobility/Bakfiets-F26/mechanical/cad-2024/scrap bike parts/rear wheel.SLDPRT

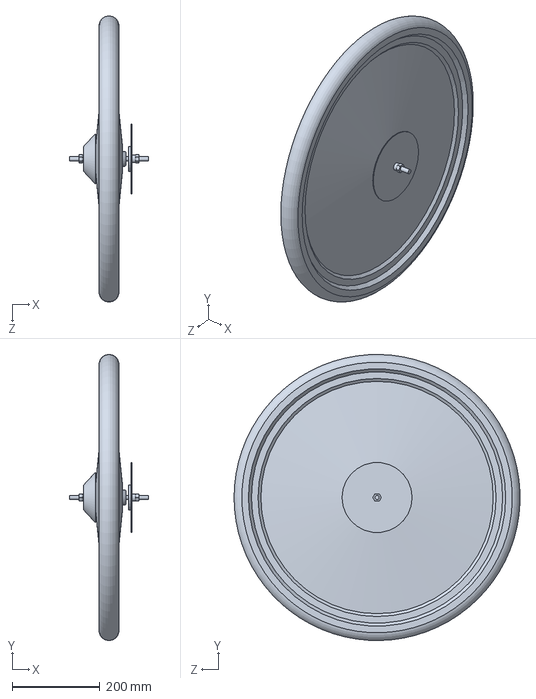
[picture p124: CAD file, 2026-09-26]
mechanical/cad-2024/scrap bike parts/rear wheel.SLDPRT
180.0 x 652.5 x 652.4 mm
