Electrium-Mobility/Bakfiets-F26/mechanical/cad-2024/scrap bike parts/stem parts/turnSignalCaseBottomV2.STL

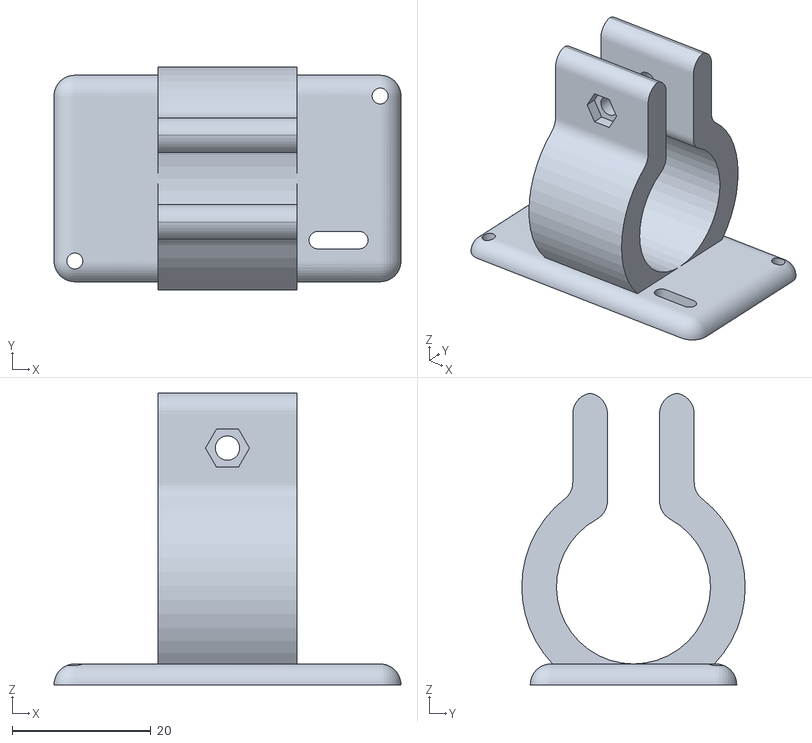
[picture p125: CAD file, 2026-09-26]
mechanical/cad-2024/scrap bike parts/stem parts/turnSignalCaseBottomV2.STL
50.0 x 32.2 x 42.0
