Electrium-Mobility/Bakfiets-F26/mechanical/cad-2024/Stays/Seat stays.SLDPRT

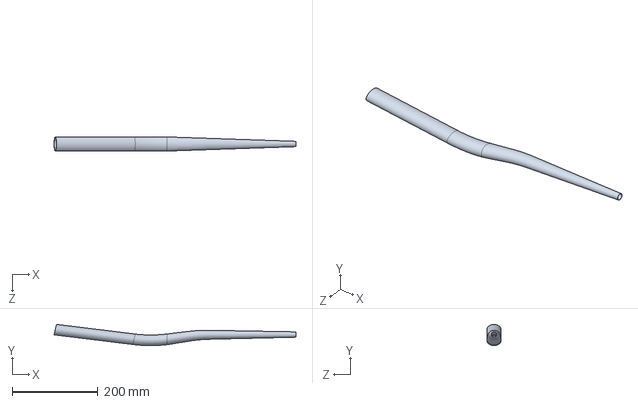
[picture p126: CAD file, 2026-09-26]
mechanical/cad-2024/Stays/Seat stays.SLDPRT
563.0 x 49.4 x 33.0 mm
