Electrium-Mobility/Bakfiets-F26/mechanical/cad-2024/steering system/clamp.SLDPRT

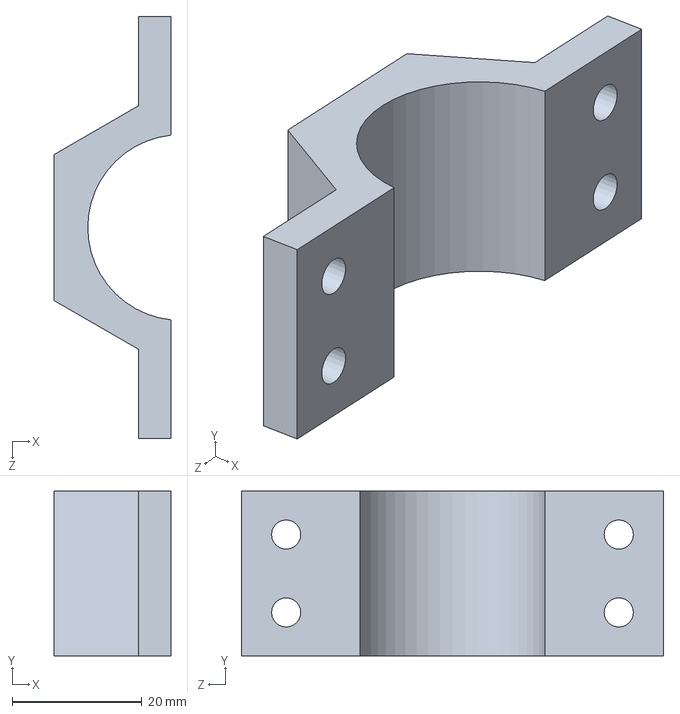
[picture p127: CAD file, 2026-09-26]
mechanical/cad-2024/steering system/clamp.SLDPRT
18.0 x 25.4 x 65.0 mm
