Electrium-Mobility/Bakfiets-F26/mechanical/cad-2025-coop/bakfiets_steering_handlebars.SLDPRT

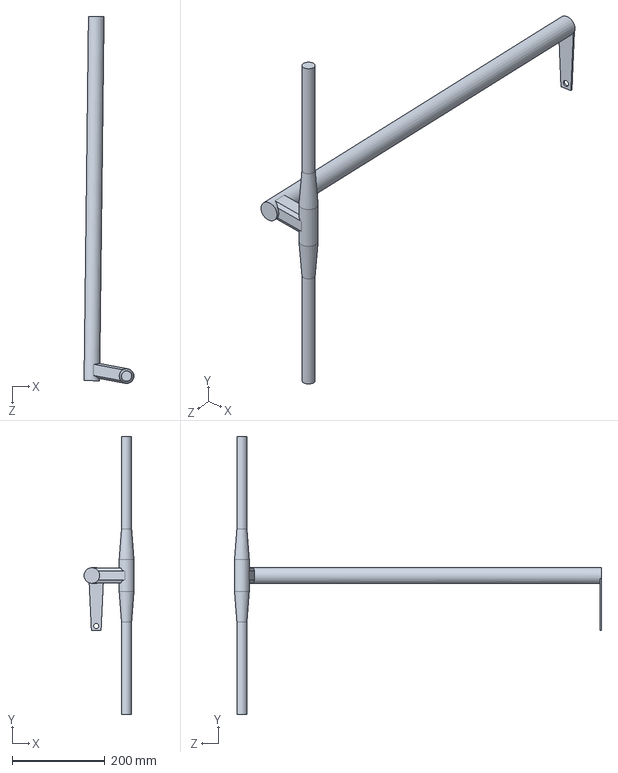
[picture p128: CAD file, 2026-09-26]
mechanical/cad-2025-coop/bakfiets_steering_handlebars.SLDPRT
107.9 x 600.0 x 792.1 mm
