Electrium-Mobility/Bakfiets-F26/mechanical/cad-2024/Frame 2.0.SLDPRT

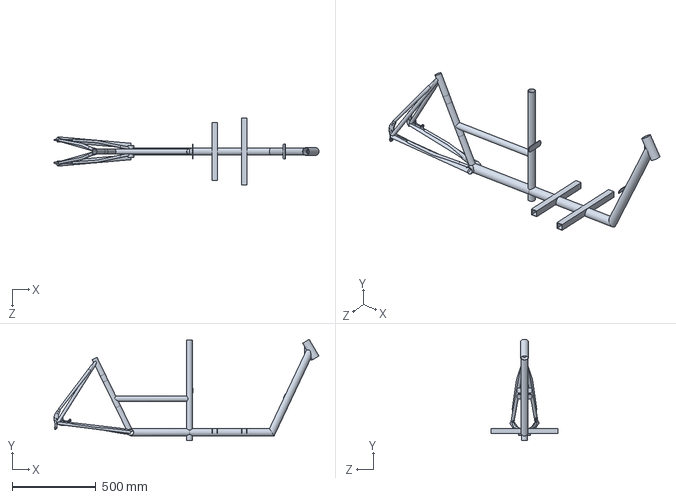
[picture p129: CAD file, 2026-09-26]
mechanical/cad-2024/Frame 2.0.SLDPRT
1580.8 x 604.2 x 400.0 mm
