Electrium-Mobility/Bakfiets-F26/mechanical/cad-2024/jig/Jig/ChainStaySupport2.SLDPRT

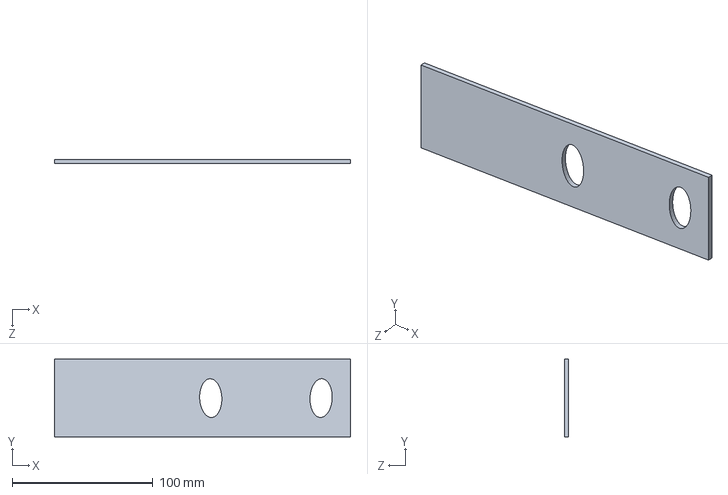
[picture p130: CAD file, 2026-09-26]
mechanical/cad-2024/jig/Jig/ChainStaySupport2.SLDPRT
210.0 x 55.0 x 3.17 mm
