Electrium-Mobility/Bakfiets-F26/mechanical/cad-2024/scrap bike parts/front fork parts/3 hole connecting part.SLDPRT

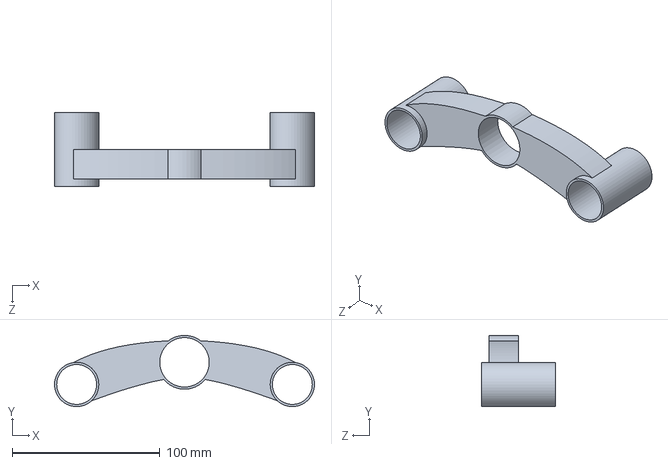
[picture p131: CAD file, 2026-09-26]
mechanical/cad-2024/scrap bike parts/front fork parts/3 hole connecting part.SLDPRT
176.0 x 48.2 x 50.0 mm
