Electrium-Mobility/Bakfiets-F26/mechanical/cad-2024/scrap bike parts/front wheel.SLDPRT

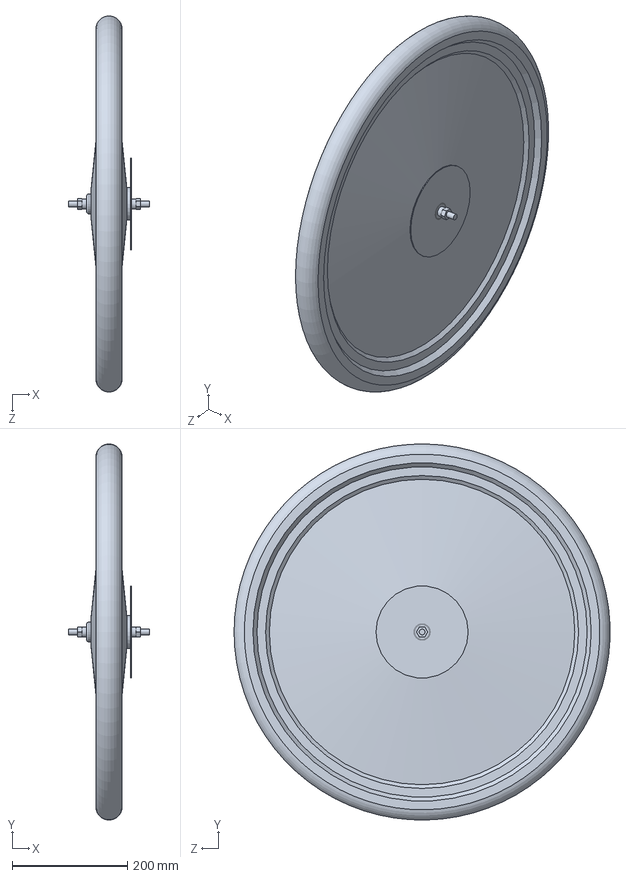
[picture p132: CAD file, 2026-09-26]
mechanical/cad-2024/scrap bike parts/front wheel.SLDPRT
140.0 x 652.5 x 652.4 mm
