Electrium-Mobility/Bakfiets-F26/mechanical/cad-2024/scrap bike parts/stem parts/handlebars rod.SLDPRT

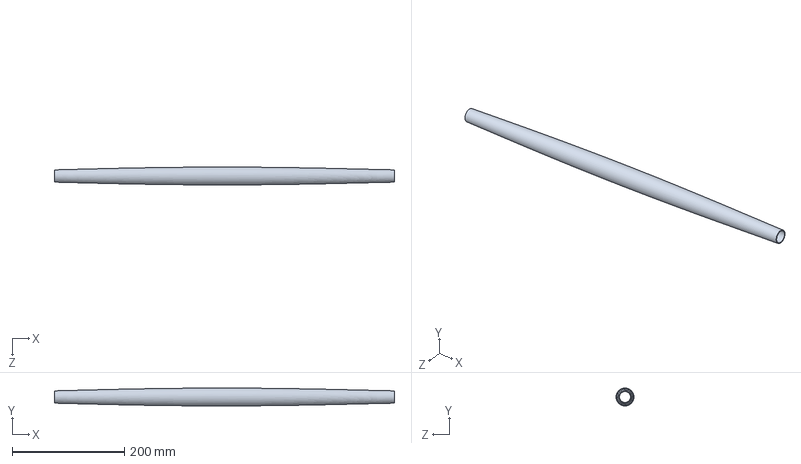
[picture p133: CAD file, 2026-09-26]
mechanical/cad-2024/scrap bike parts/stem parts/handlebars rod.SLDPRT
607.1 x 31.9 x 31.9 mm
