Electrium-Mobility/Bakfiets-F26/mechanical/cad-2024/steering system/ball joint/ball.SLDPRT

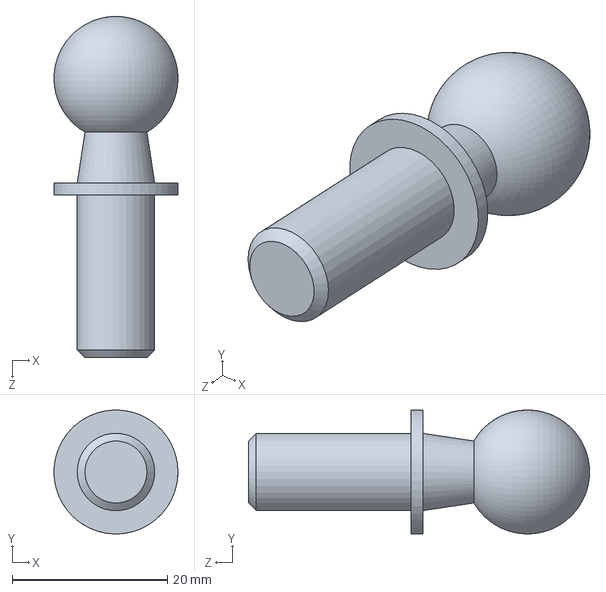
[picture p134: CAD file, 2026-09-26]
mechanical/cad-2024/steering system/ball joint/ball.SLDPRT
16.0 x 16.0 x 44.0 mm
