Electrium-Mobility/Bakfiets-F26/mechanical/cad-2024/steering system/steering shaft.SLDPRT

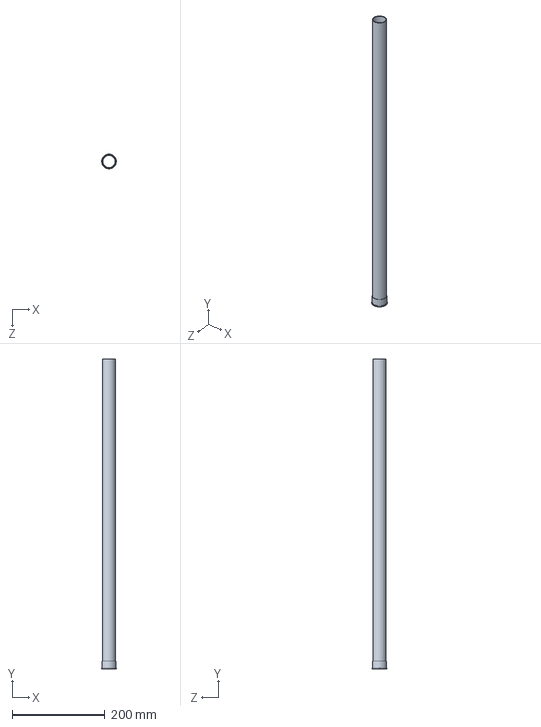
[picture p135: CAD file, 2026-09-26]
mechanical/cad-2024/steering system/steering shaft.SLDPRT
31.7 x 667.0 x 31.7 mm
