Electrium-Mobility/Bakfiets-F26/mechanical/cad-2025-coop/bakfiets_front_wheel.SLDPRT

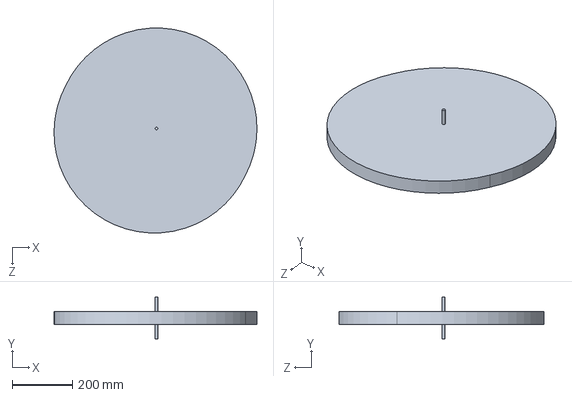
[picture p136: CAD file, 2026-09-26]
mechanical/cad-2025-coop/bakfiets_front_wheel.SLDPRT
676.6 x 139.0 x 682.6 mm
