Electrium-Mobility/Bakfiets-F26/mechanical/cad-2025-coop/edited-2024-parts/Custom Angle for Sides 2.SLDPRT

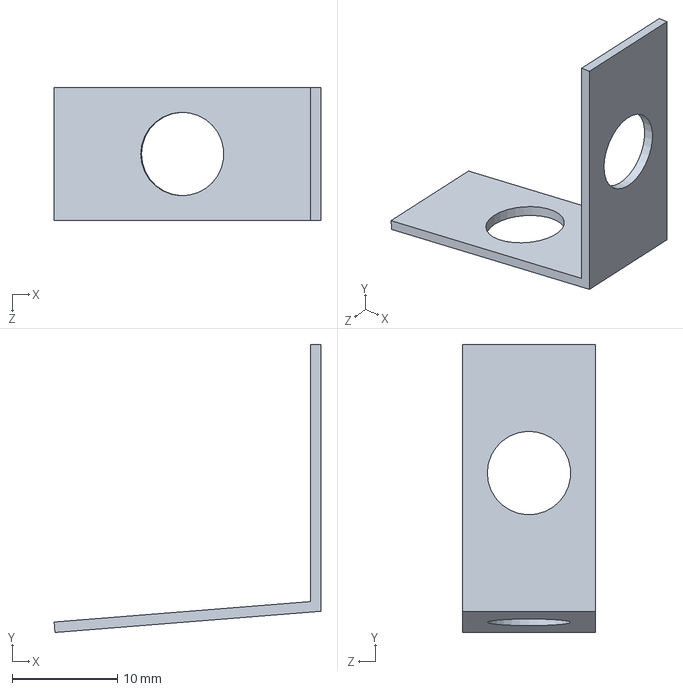
[picture p137: CAD file, 2026-09-26]
mechanical/cad-2025-coop/edited-2024-parts/Custom Angle for Sides 2.SLDPRT
25.4 x 27.4 x 12.7 mm
