Electrium-Mobility/Bakfiets-F26/mechanical/cad-2024/Cargo Box 2.SLDPRT

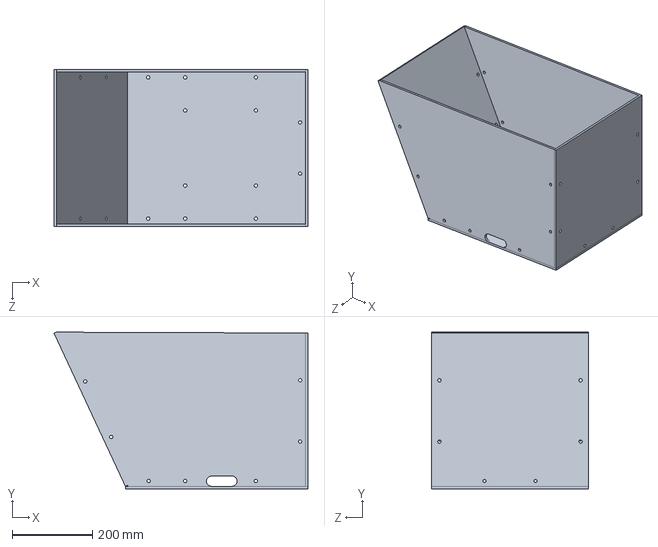
[picture p138: CAD file, 2026-09-26]
mechanical/cad-2024/Cargo Box 2.SLDPRT
631.5 x 389.6 x 390.0 mm
