Electrium-Mobility/Bakfiets-F26/mechanical/cad-2024/jig/Jig/bottomGuide.DXF

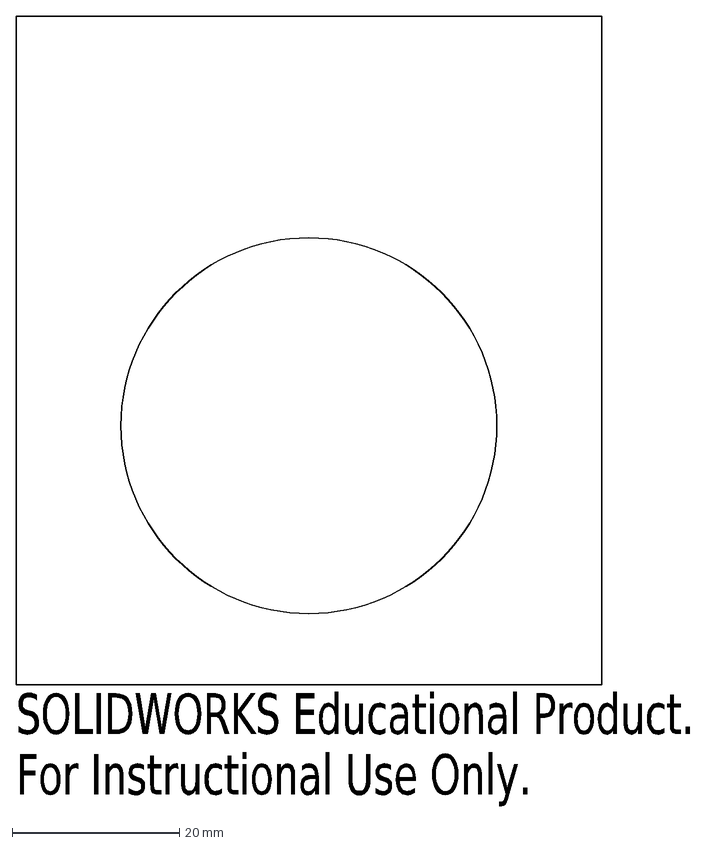
[picture p139: CAD file, 2026-09-26]
mechanical/cad-2024/jig/Jig/bottomGuide.DXF
SOLIDWORKS Educational Product.
For Instructional Use Only.
