Electrium-Mobility/Bakfiets-F26/mechanical/cad-2024/MotorCrank/Crank Wheel.SLDPRT

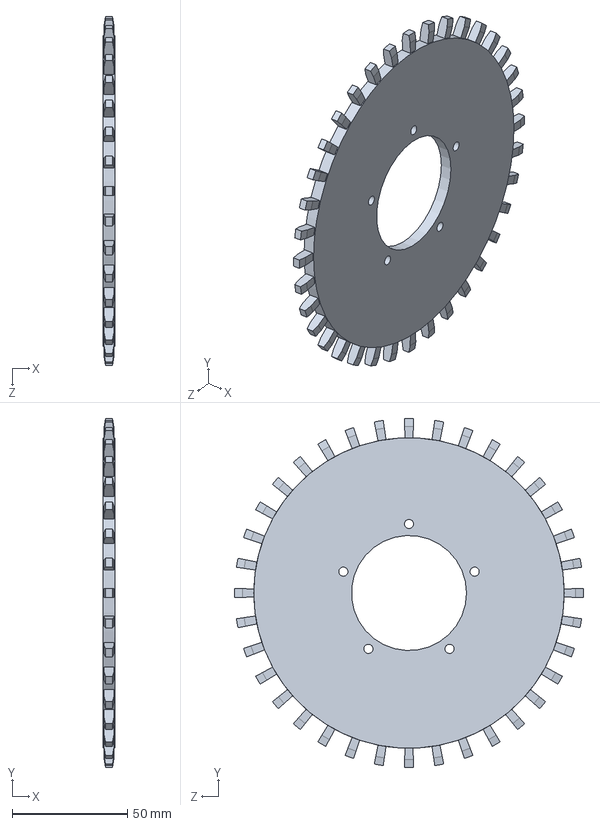
[picture p140: CAD file, 2026-09-26]
mechanical/cad-2024/MotorCrank/Crank Wheel.SLDPRT
5.03 x 151.7 x 151.7 mm
