Electrium-Mobility/Bakfiets-F26/mechanical/cad-2024/scrap bike parts/front fork parts/top rod fork.SLDPRT

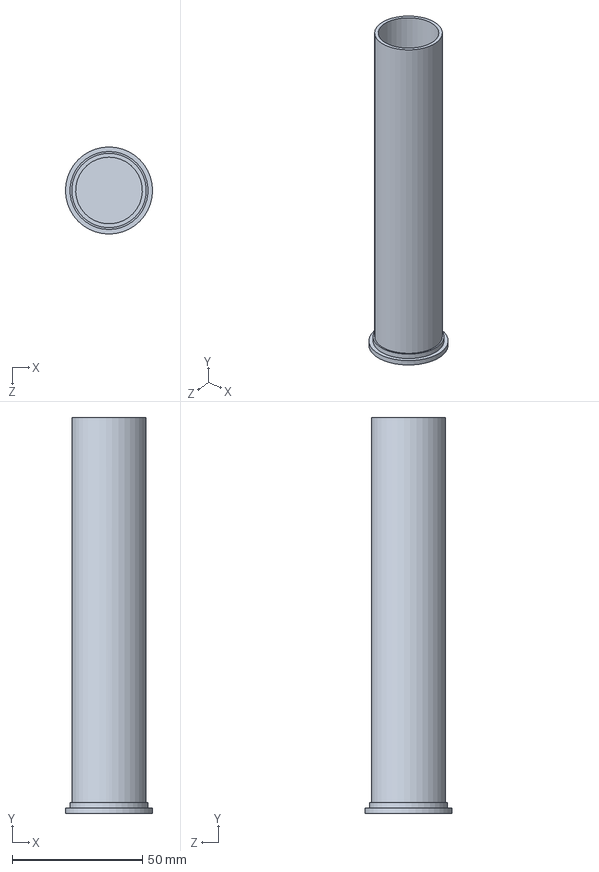
[picture p141: CAD file, 2026-09-26]
mechanical/cad-2024/scrap bike parts/front fork parts/top rod fork.SLDPRT
33.5 x 152.2 x 33.5 mm
