Electrium-Mobility/Bakfiets-F26/mechanical/cad-2025-coop/edited-2024-parts/Aluminum Angle (1.25 x 0.125).SLDPRT

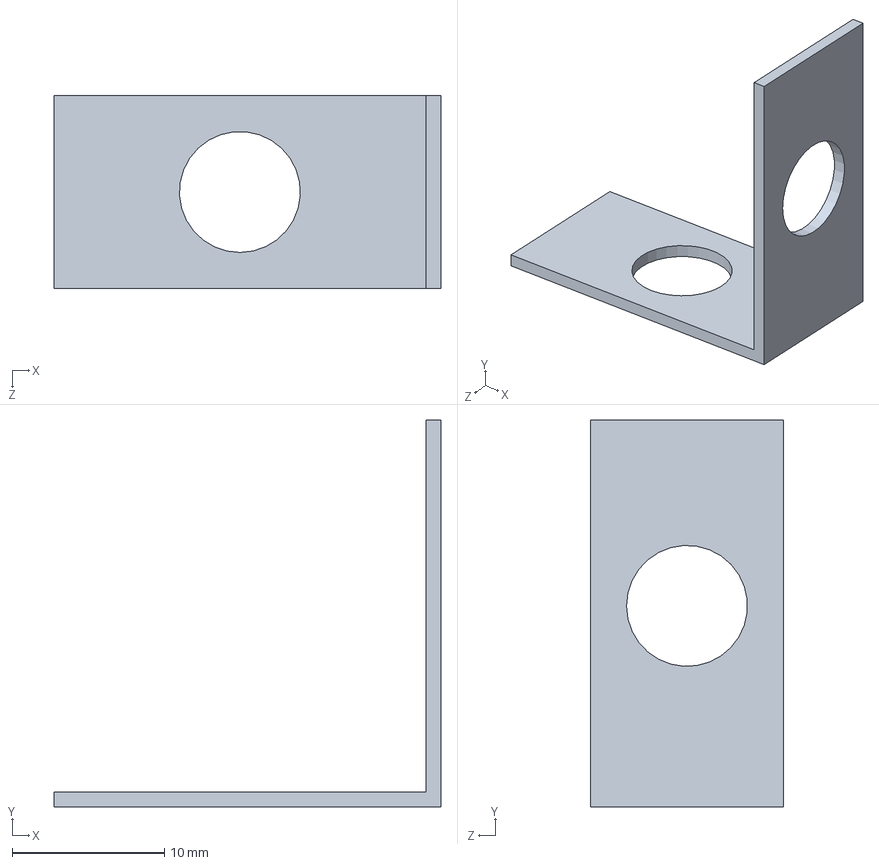
[picture p142: CAD file, 2026-09-26]
mechanical/cad-2025-coop/edited-2024-parts/Aluminum Angle (1.25 x 0.125).SLDPRT
25.4 x 25.4 x 12.7 mm
