Electrium-Mobility/Bakfiets-F26/mechanical/cad-2024/MotorCrank/Motor.SLDPRT

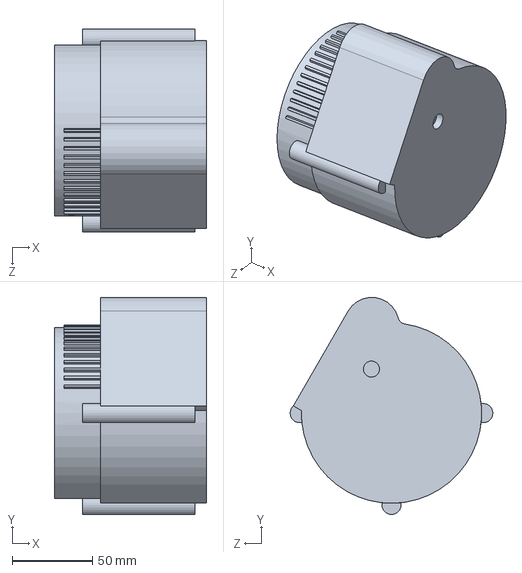
[picture p144: CAD file, 2026-09-26]
mechanical/cad-2024/MotorCrank/Motor.SLDPRT
94.6 x 135.1 x 126.2 mm
