Electrium-Mobility/Bakfiets-F26/mechanical/cad-2024/scrap bike parts/front fork parts/front fork.SLDPRT

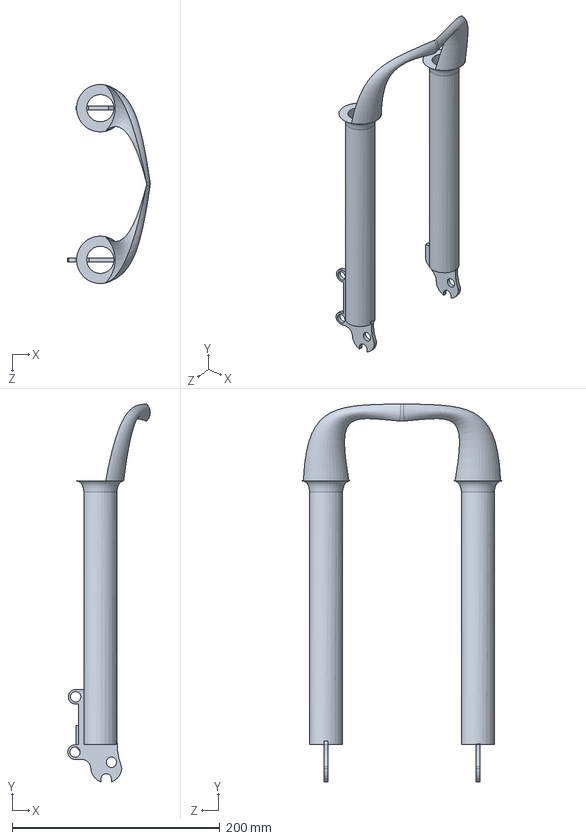
[picture p145: CAD file, 2026-09-26]
mechanical/cad-2024/scrap bike parts/front fork parts/front fork.SLDPRT
79.5 x 363.9 x 191.7 mm
