Electrium-Mobility/Bakfiets-F26/mechanical/cad-2024/scrap bike parts/stem parts/stem.SLDPRT

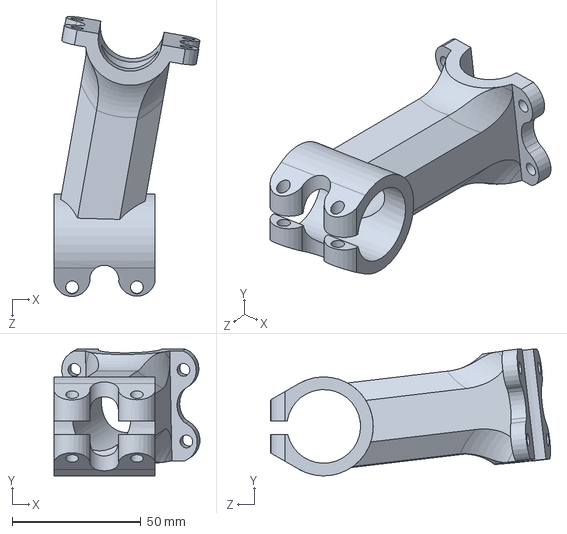
[picture p146: CAD file, 2026-09-26]
mechanical/cad-2024/scrap bike parts/stem parts/stem.SLDPRT
56.6 x 49.3 x 108.7 mm
