Electrium-Mobility/Bakfiets-F26/mechanical/cad-2025-coop/bakfiets_steering_rod.SLDPRT

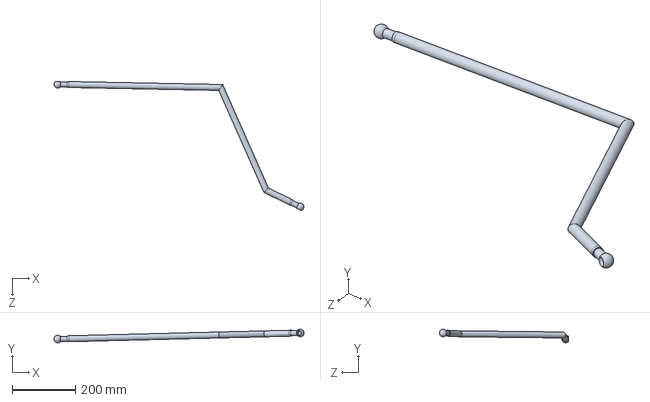
[picture p147: CAD file, 2026-09-26]
mechanical/cad-2025-coop/bakfiets_steering_rod.SLDPRT
789.9 x 43.0 x 407.8 mm
