Electrium-Mobility/Bakfiets-F26/mechanical/cad-2024/Circular tubing frame (COPY).DXF

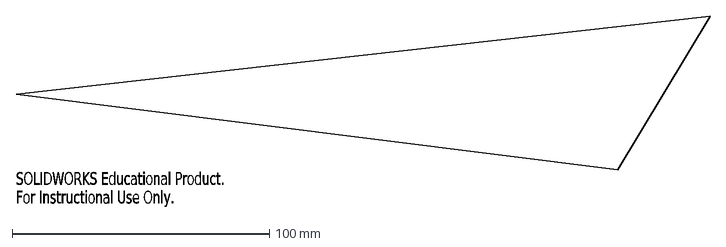
[picture p148: CAD file, 2026-09-26]
mechanical/cad-2024/Circular tubing frame (COPY).DXF
SOLIDWORKS Educational Product.
For Instructional Use Only.
