Electrium-Mobility/Bakfiets-F26/mechanical/cad-2024/MotorCrank/Crank'.SLDPRT

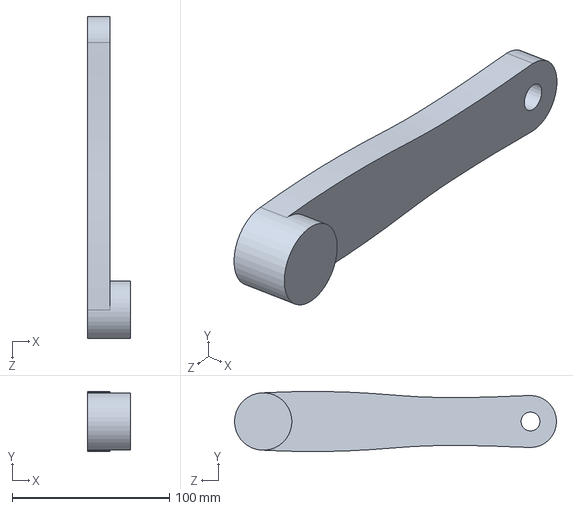
[picture p149: CAD file, 2026-09-26]
mechanical/cad-2024/MotorCrank/Crank'.SLDPRT
27.1 x 38.1 x 204.5 mm
