Electrium-Mobility/Bakfiets-F26/mechanical/cad-2024/scrap bike parts/stem parts/turnSignalCase.SLDPRT

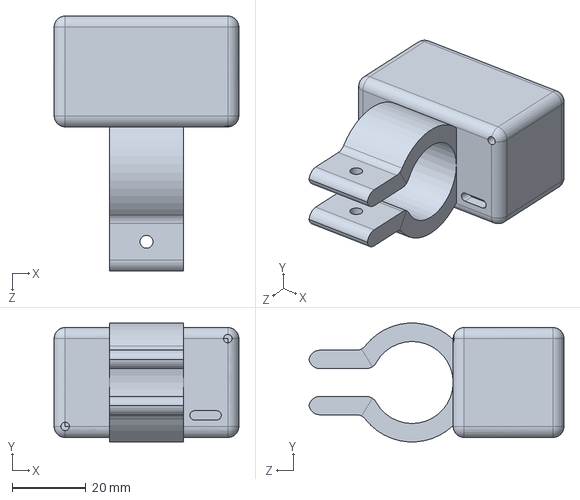
[picture p150: CAD file, 2026-09-26]
mechanical/cad-2024/scrap bike parts/stem parts/turnSignalCase.SLDPRT
50.0 x 32.1 x 69.0 mm
