Electrium-Mobility/Bakfiets-F26/mechanical/cad-2025-coop/bakfiets_ball_joint.SLDPRT

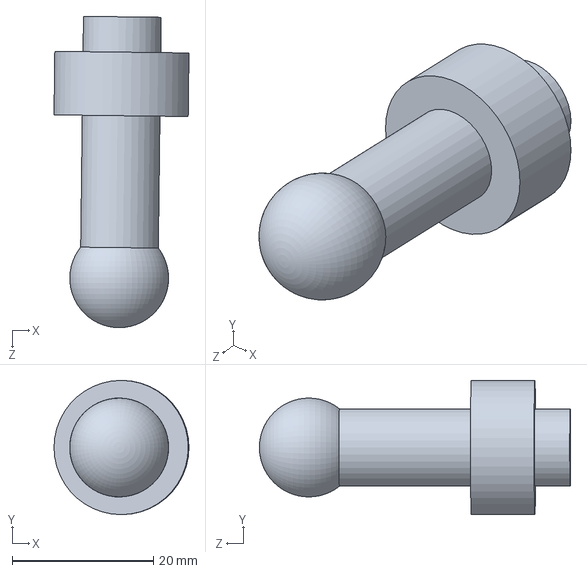
[picture p151: CAD file, 2026-09-26]
mechanical/cad-2025-coop/bakfiets_ball_joint.SLDPRT
19.1 x 19.0 x 44.1 mm
