Electrium-Mobility/Bakfiets-F26/mechanical/cad-2024/jig/Jig/JigCone.SLDPRT

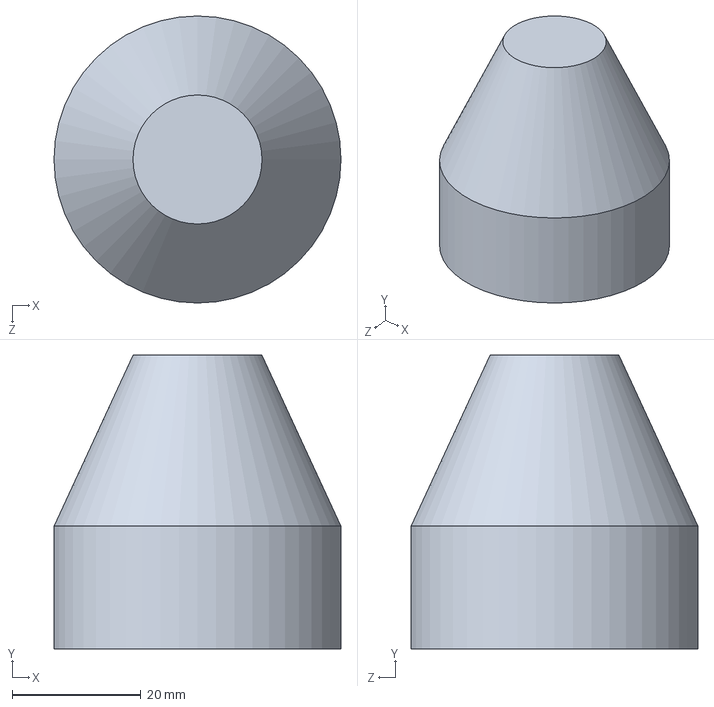
[picture p152: CAD file, 2026-09-26]
mechanical/cad-2024/jig/Jig/JigCone.SLDPRT
44.5 x 45.5 x 44.5 mm
