Electrium-Mobility/Bakfiets-F26/mechanical/cad-2024/scrap bike parts/stem parts/turnSignalCaseTop.STL

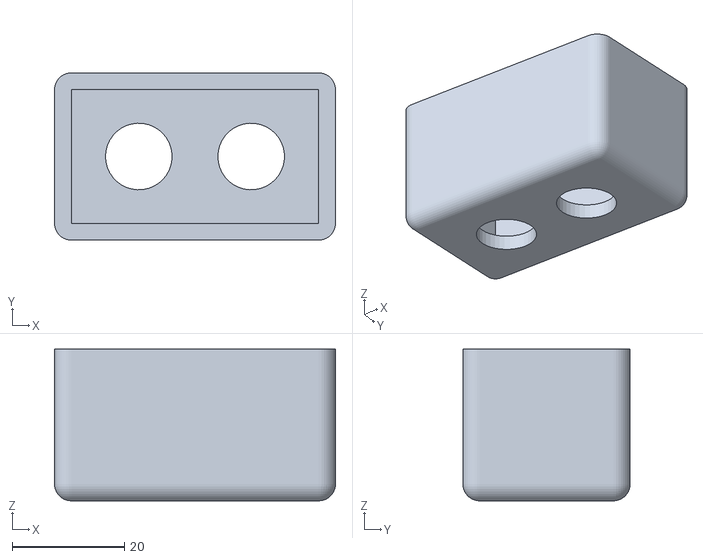
[picture p153: CAD file, 2026-09-26]
mechanical/cad-2024/scrap bike parts/stem parts/turnSignalCaseTop.STL
50.0 x 29.8 x 27.0
