Electrium-Mobility/Bakfiets-F26/mechanical/cad-2024/steering system/rear steering plate.SLDPRT

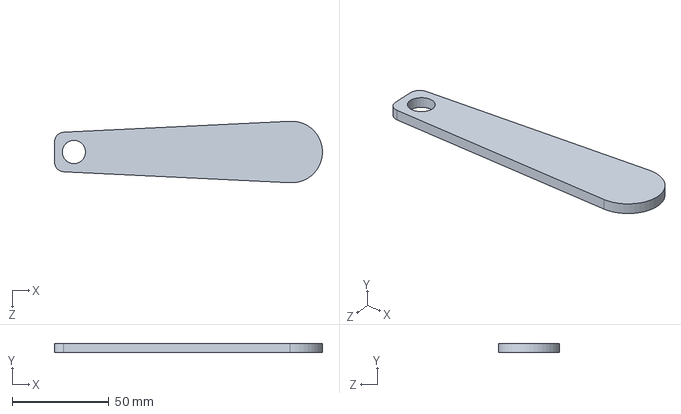
[picture p154: CAD file, 2026-09-26]
mechanical/cad-2024/steering system/rear steering plate.SLDPRT
138.3 x 4.76 x 31.7 mm
