Electrium-Mobility/Bakfiets-F26/mechanical/cad-2024/scrap bike parts/stem parts/top stem.SLDPRT

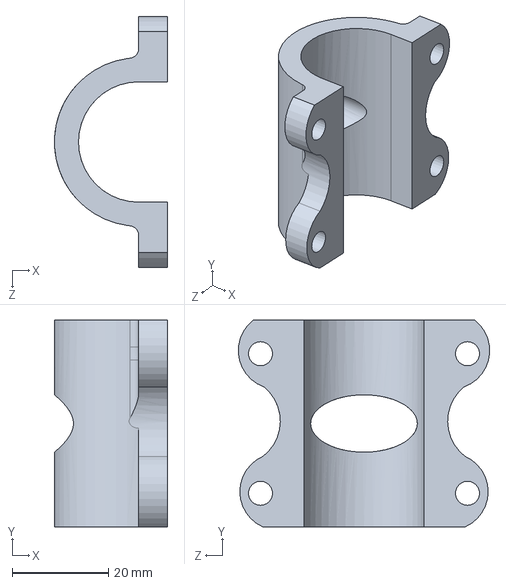
[picture p155: CAD file, 2026-09-26]
mechanical/cad-2024/scrap bike parts/stem parts/top stem.SLDPRT
23.5 x 43.0 x 52.2 mm
