Electrium-Mobility/Bakfiets-F26/mechanical/cad-2024/steering system/steeringLink-Split1.SLDPRT

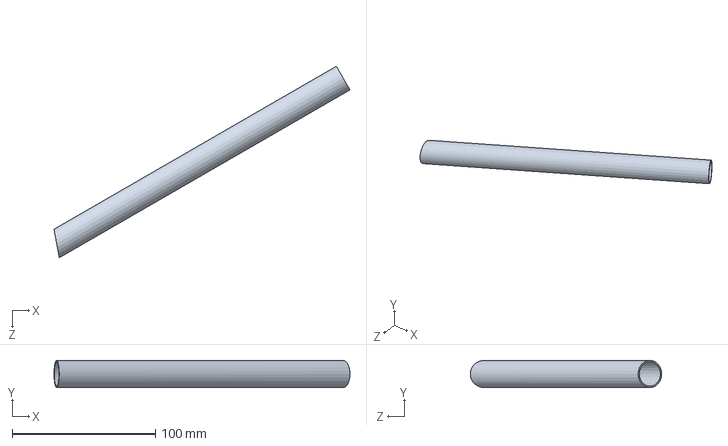
[picture p156: CAD file, 2026-09-26]
mechanical/cad-2024/steering system/steeringLink-Split1.SLDPRT
206.6 x 19.1 x 133.7 mm
