Electrium-Mobility/Bakfiets-F26/mechanical/cad-2025-coop/bakfiets_frame.SLDPRT

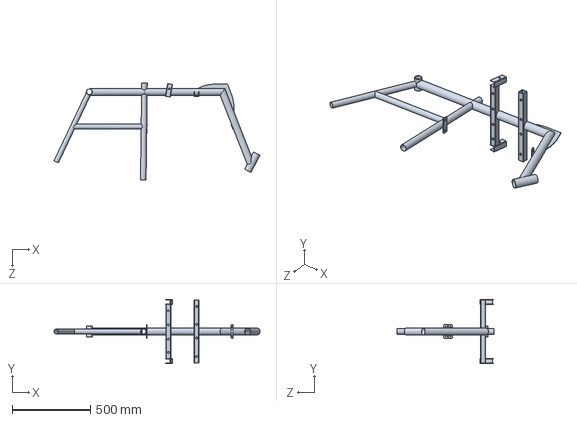
[picture p157: CAD file, 2026-09-26]
mechanical/cad-2025-coop/bakfiets_frame.SLDPRT
1318.2 x 410.0 x 623.4 mm
