Electrium-Mobility/Bakfiets-F26/mechanical/cad-2024/Cargo Box.SLDPRT

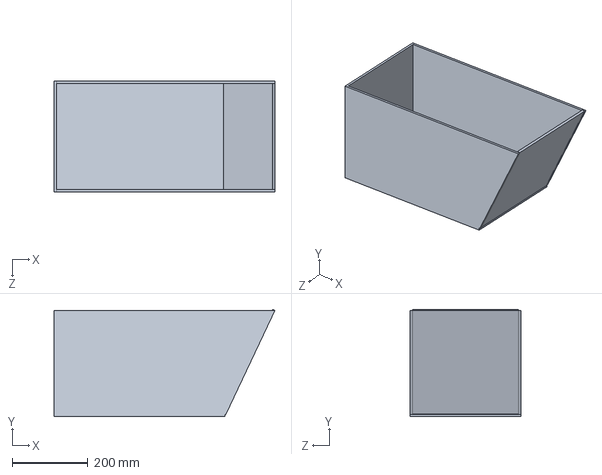
[picture p158: CAD file, 2026-09-26]
mechanical/cad-2024/Cargo Box.SLDPRT
584.9 x 284.3 x 292.6 mm
