Electrium-Mobility/Bakfiets-F26/mechanical/cad-2024/steering system/steeringLink.SLDPRT

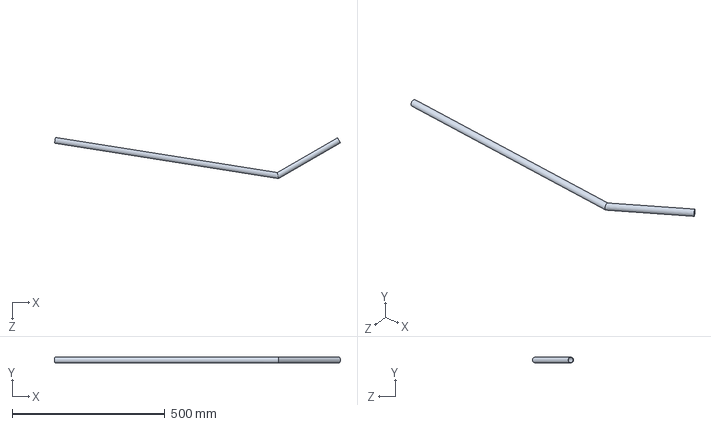
[picture p159: CAD file, 2026-09-26]
mechanical/cad-2024/steering system/steeringLink.SLDPRT
936.3 x 19.1 x 134.8 mm
