Electrium-Mobility/Bakfiets-F26/mechanical/cad-2025-coop/bakfiets_cargo_box_low_detail.SLDPRT

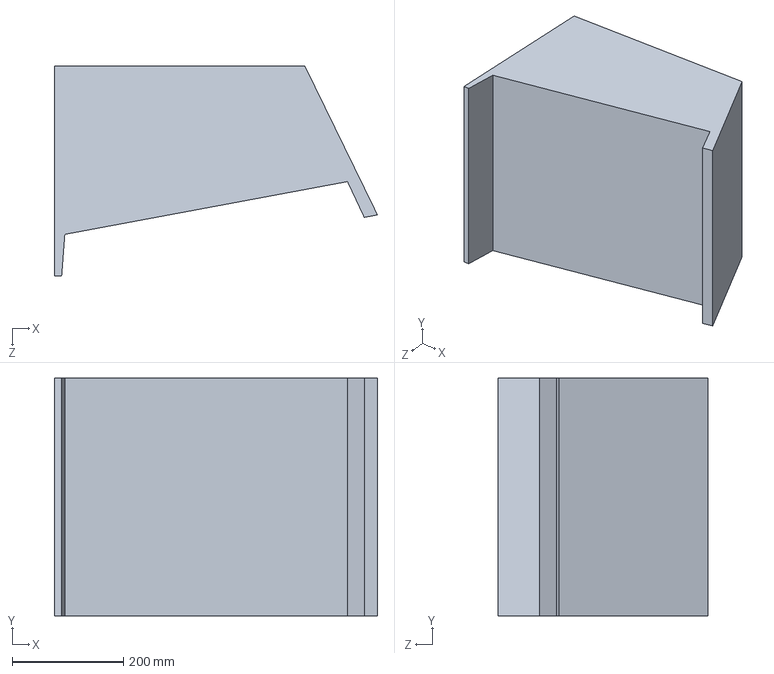
[picture p160: CAD file, 2026-09-26]
mechanical/cad-2025-coop/bakfiets_cargo_box_low_detail.SLDPRT
580.6 x 427.6 x 378.0 mm
