Electrium-Mobility/Bakfiets-F26/mechanical/cad-2025-coop/bakfiets_front_suspension.SLDPRT

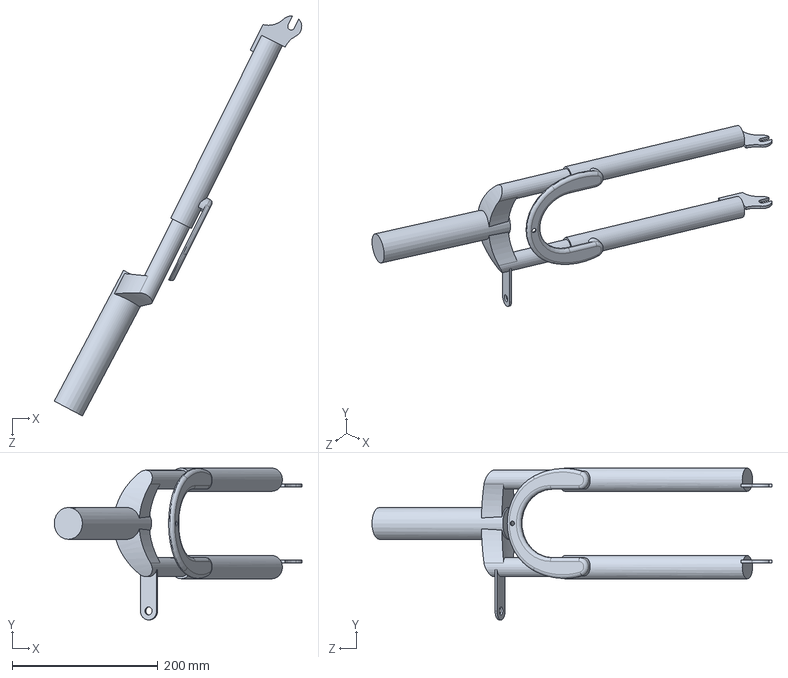
[picture p161: CAD file, 2026-09-26]
mechanical/cad-2025-coop/bakfiets_front_suspension.SLDPRT
339.6 x 208.5 x 548.8 mm
