Electrium-Mobility/Bakfiets-F26/mechanical/cad-2024/jig/Jig/SeatStaysSupport.SLDPRT

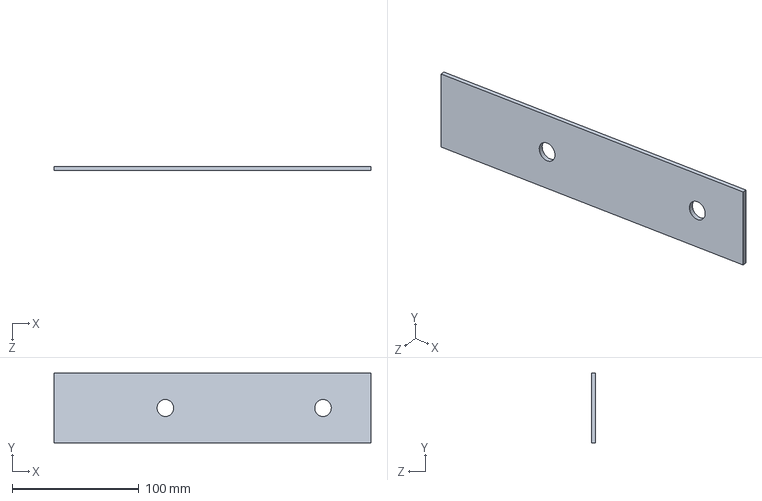
[picture p162: CAD file, 2026-09-26]
mechanical/cad-2024/jig/Jig/SeatStaysSupport.SLDPRT
250.0 x 55.0 x 3.17 mm
