Electrium-Mobility/Bakfiets-F26/mechanical/cad-2024/jig/Jig/End1.SLDPRT

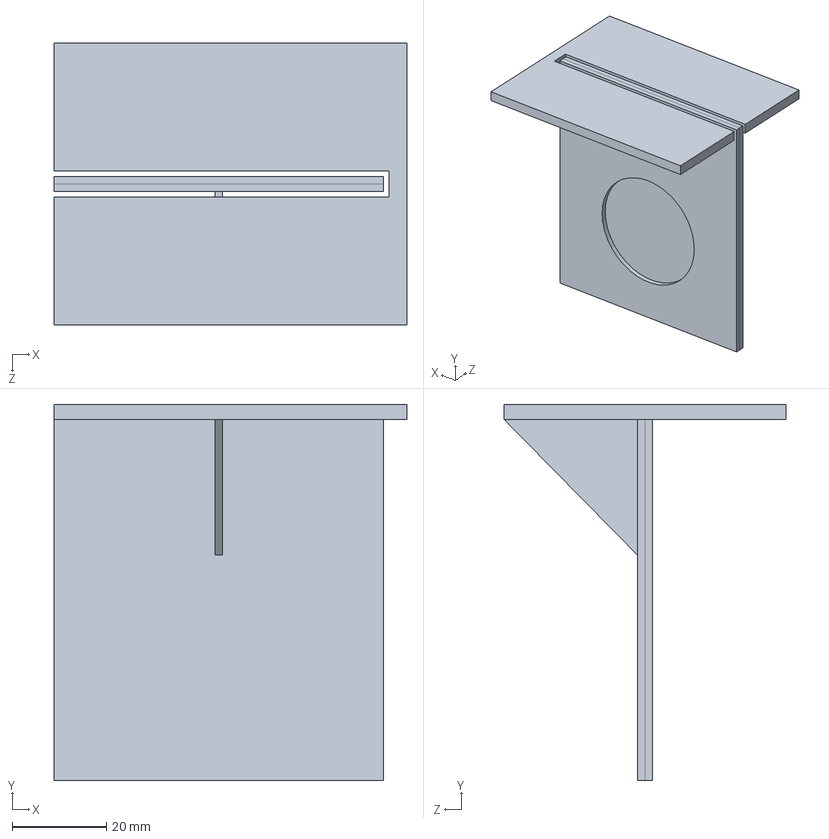
[picture p163: CAD file, 2026-09-26]
mechanical/cad-2024/jig/Jig/End1.SLDPRT
75.0 x 80.0 x 60.0 mm
