Electrium-Mobility/Bakfiets-F26/mechanical/cad-2024/Seat tube (430 mm).SLDPRT

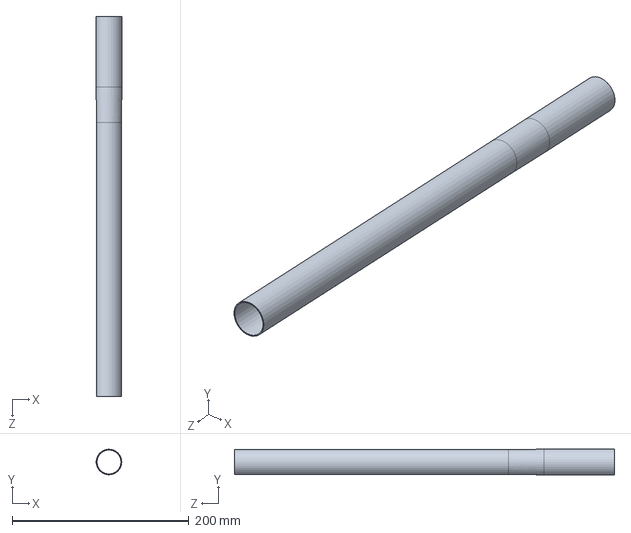
[picture p164: CAD file, 2026-09-26]
mechanical/cad-2024/Seat tube (430 mm).SLDPRT
29.0 x 29.0 x 430.0 mm
