Electrium-Mobility/Bakfiets-F26/mechanical/cad-2024/Custom Angle for Sides 3.SLDPRT

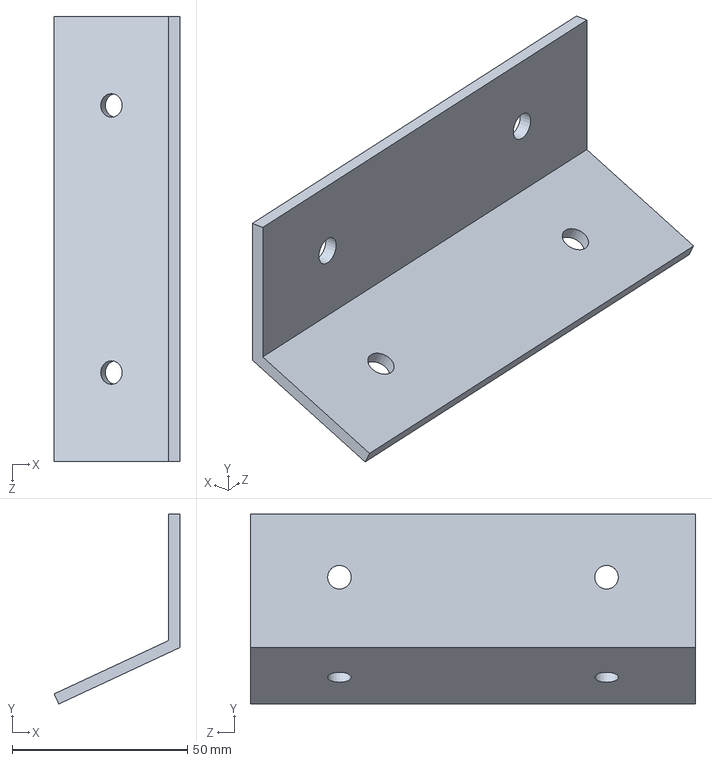
[picture p165: CAD file, 2026-09-26]
mechanical/cad-2024/Custom Angle for Sides 3.SLDPRT
35.9 x 54.2 x 127.0 mm
