Electrium-Mobility/Bakfiets-F26/mechanical/cad-2024/jig/Jig/Gusset.SLDPRT

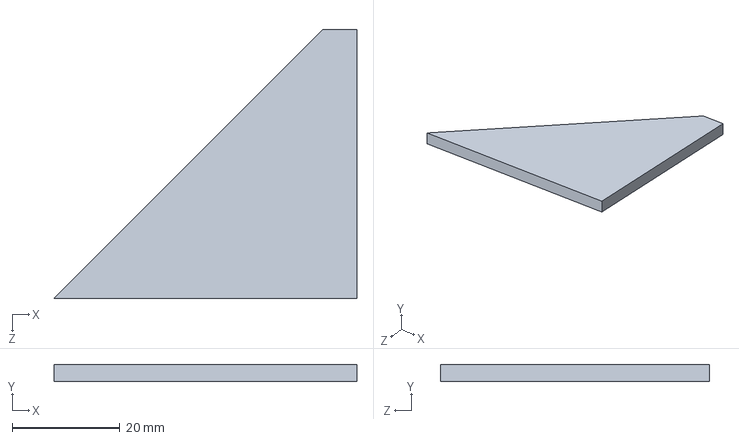
[picture p166: CAD file, 2026-09-26]
mechanical/cad-2024/jig/Jig/Gusset.SLDPRT
56.3 x 3.17 x 50.0 mm
