Electrium-Mobility/Bakfiets-F26/mechanical/cad-2024/KickstandBracketFeb15.SLDPRT

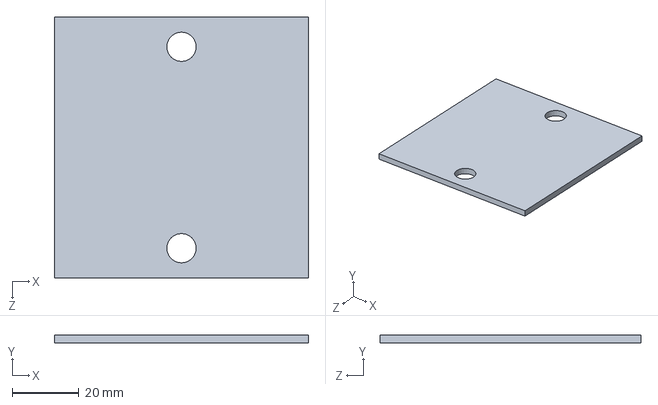
[picture p168: CAD file, 2026-09-26]
mechanical/cad-2024/KickstandBracketFeb15.SLDPRT
76.2 x 2.54 x 78.2 mm
