Electrium-Mobility/Bakfiets-F26/mechanical/cad-2024/jig/Jig/endRib.DXF

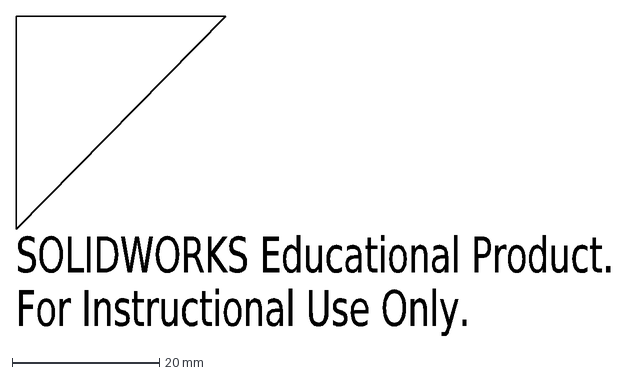
[picture p170: CAD file, 2026-09-26]
mechanical/cad-2024/jig/Jig/endRib.DXF
SOLIDWORKS Educational Product.
For Instructional Use Only.
