Electrium-Mobility/Bakfiets-F26/mechanical/cad-2024/Top tube (460mm).SLDPRT

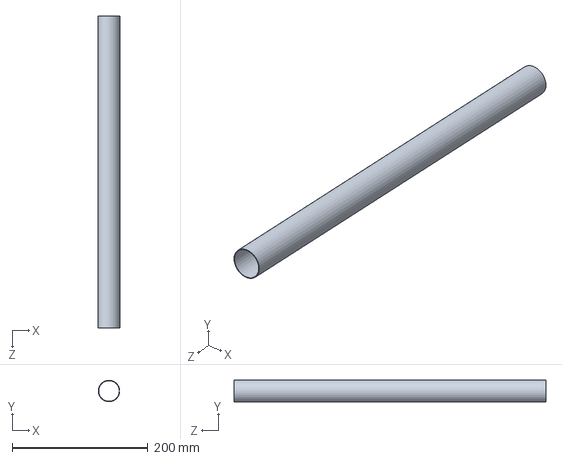
[picture p171: CAD file, 2026-09-26]
mechanical/cad-2024/Top tube (460mm).SLDPRT
31.7 x 31.7 x 460.0 mm
