Electrium-Mobility/Bakfiets-F26/mechanical/cad-2024/jig/Jig/ConeSupportConnector.SLDPRT

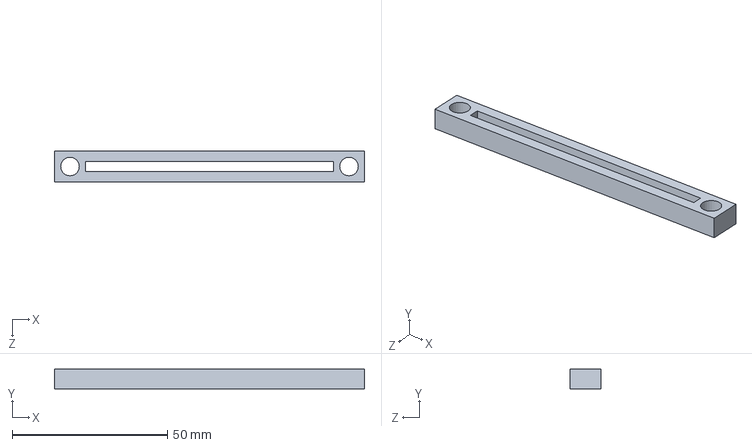
[picture p172: CAD file, 2026-09-26]
mechanical/cad-2024/jig/Jig/ConeSupportConnector.SLDPRT
100.0 x 6.35 x 10.0 mm
