Electrium-Mobility/Bakfiets-F26/mechanical/cad-2024/jig/Jig/SteeringTubeSupport.SLDPRT

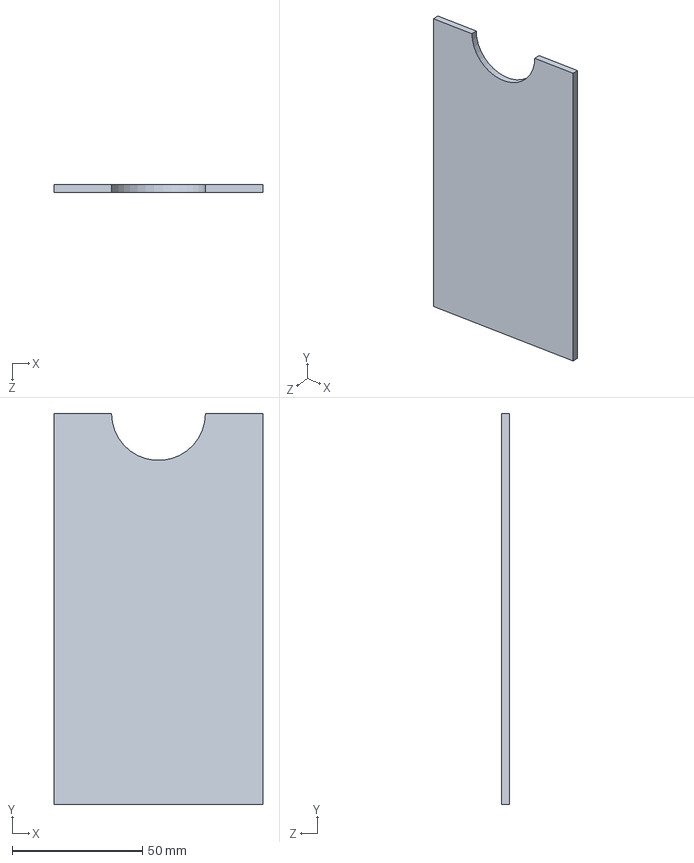
[picture p174: CAD file, 2026-09-26]
mechanical/cad-2024/jig/Jig/SteeringTubeSupport.SLDPRT
80.0 x 150.0 x 3.17 mm
