Electrium-Mobility/Bakfiets-F26/mechanical/cad-2024/jig/Jig/Part11^JigV2.DXF

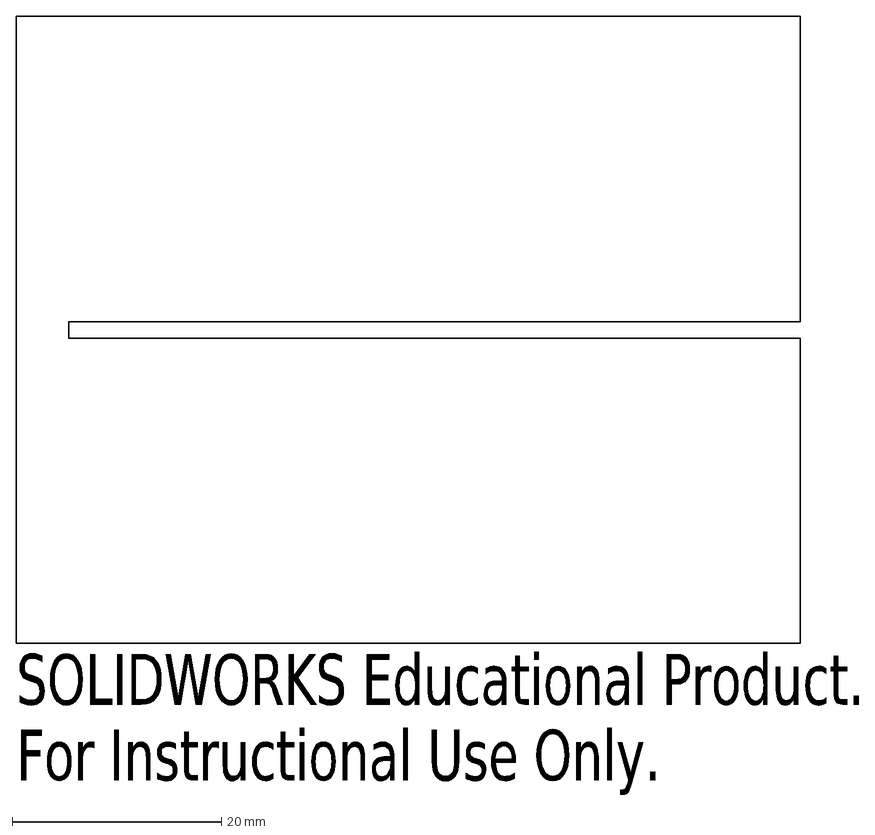
[picture p177: CAD file, 2026-09-26]
mechanical/cad-2024/jig/Jig/Part11^JigV2.DXF
SOLIDWORKS Educational Product.
For Instructional Use Only.
