Electrium-Mobility/Bakfiets-F26/mechanical/cad-2024/jig/Jig/ConeSupportPiece.SLDPRT

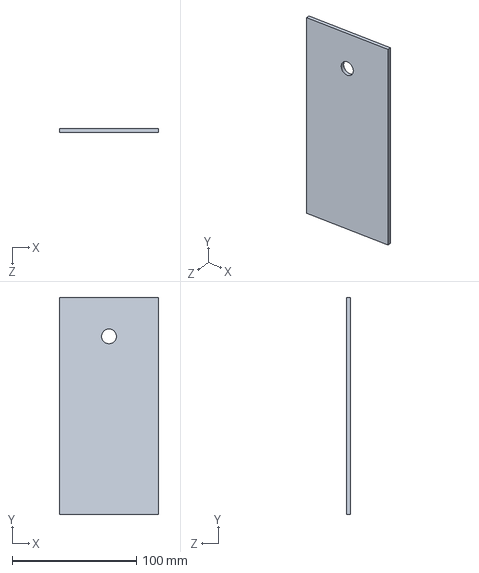
[picture p178: CAD file, 2026-09-26]
mechanical/cad-2024/jig/Jig/ConeSupportPiece.SLDPRT
80.0 x 175.0 x 3.17 mm
