Electrium-Mobility/Bakfiets-F26/mechanical/cad-2024/jig/Jig/JigBaseMDFNew2.SLDPRT

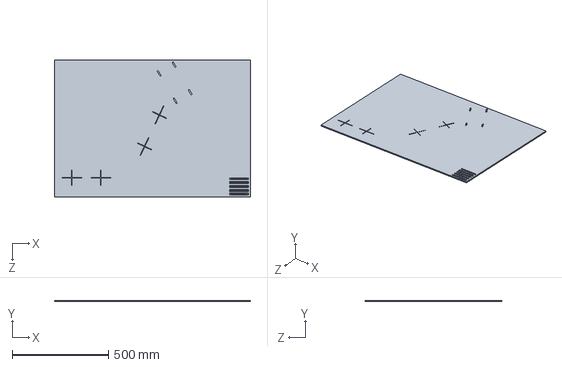
[picture p179: CAD file, 2026-09-26]
mechanical/cad-2024/jig/Jig/JigBaseMDFNew2.SLDPRT
1016.0 x 6.35 x 711.2 mm
