Electrium-Mobility/Bakfiets-F26/mechanical/cad-2024/jig/Jig/RearDropoutBracket.SLDPRT

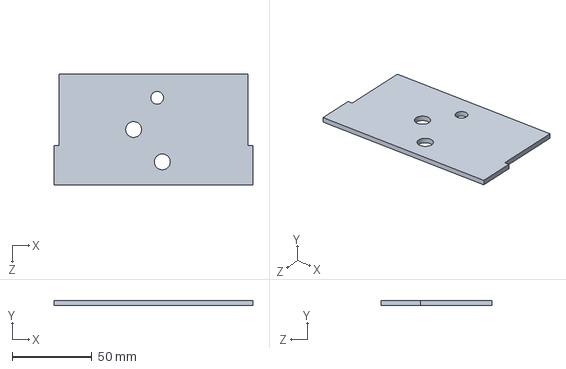
[picture p180: CAD file, 2026-09-26]
mechanical/cad-2024/jig/Jig/RearDropoutBracket.SLDPRT
125.0 x 3.17 x 70.0 mm
