Electrium-Mobility/Bakfiets-F26/mechanical/cad-2024/jig/Jig/BottomBracketSupport.SLDPRT

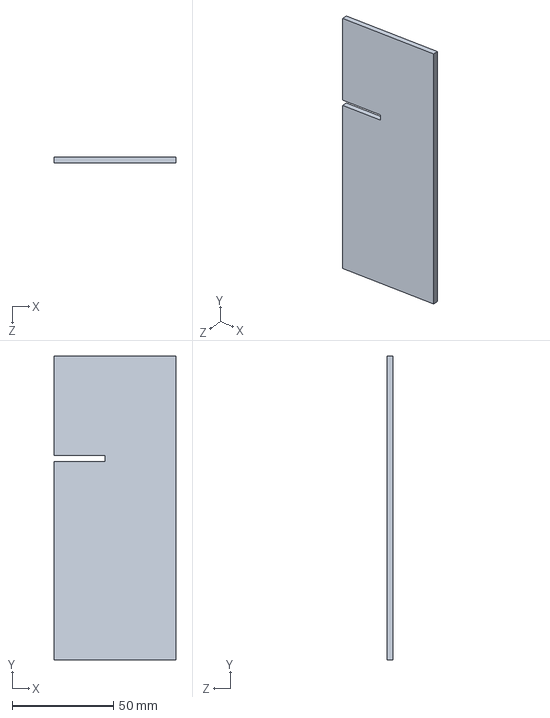
[picture p182: CAD file, 2026-09-26]
mechanical/cad-2024/jig/Jig/BottomBracketSupport.SLDPRT
60.0 x 150.0 x 3.17 mm
