Electrium-Mobility/Bakfiets-F26/mechanical/cad-2024/jig/Jig/RearDropoutSupport.SLDPRT

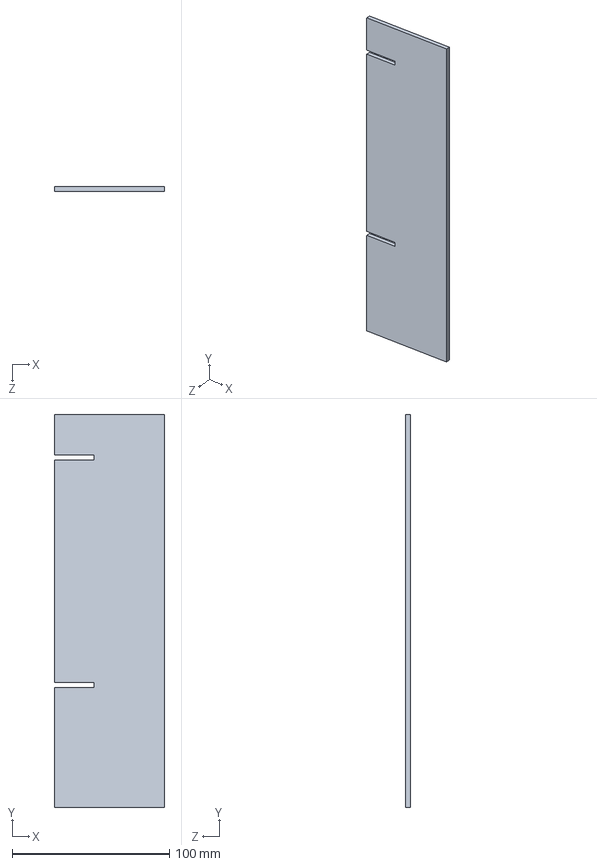
[picture p183: CAD file, 2026-09-26]
mechanical/cad-2024/jig/Jig/RearDropoutSupport.SLDPRT
70.0 x 250.0 x 3.17 mm
