Electrium-Mobility/Bakfiets-F26/mechanical/cad-2024/jig/Jig/JigAssemblyMarch16.SLDASM

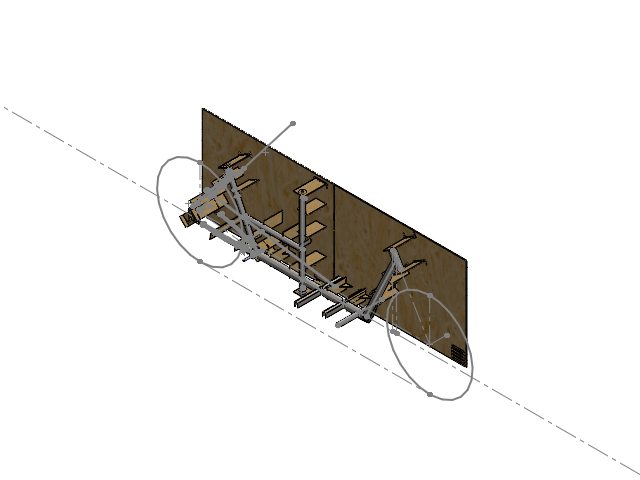
[picture p192: CAD file, 2026-09-26]
mechanical/cad-2024/jig/Jig/JigAssemblyMarch16.SLDASM
Frame 2.0
JigBaseMDFNew1
JigBaseMDFNew2
BottomBracketClamp
SteeringTubeSupport x 3
TopTubeSupport x 4
BottomBracketSupport x 2
RearDropoutBracket x 2
RearDropoutSupport x 2
Gusset x 12
JigCone x 3
ConeSupportConnector x 5
ConeSupportPiece x 5
SeatStaysSupport
ChainStaySupport1
ChainStaySupport2
