Electrium-Mobility/Bakfiets-F26/mechanical/cad-2024/notches/Notching Assembly.SLDASM

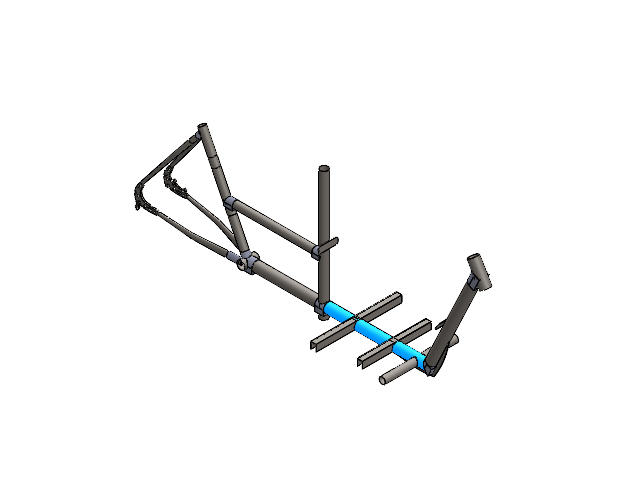
[picture p193: CAD file, 2026-09-26]
mechanical/cad-2024/notches/Notching Assembly.SLDASM
Frame 2.0
Seat Tube to BB
Chain Stay R
Chain Stay L
Top Tube to ST
Seat Stay L
Seat Stay R
Main Tube to HT
Top Tube to SeT
Main Tube to BB
Main Tube to StT
Main Tube to MTH
Main Tube H to MT
