Electrium-Mobility/Bakfiets-F26/mechanical/cad-2024/KickstandAssembly.SLDASM

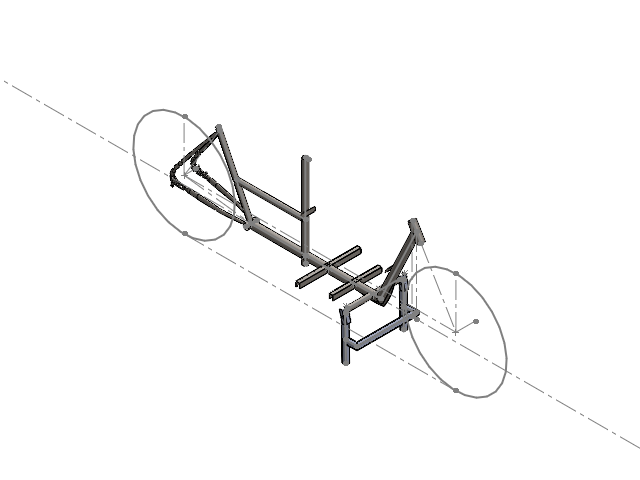
[picture p194: CAD file, 2026-09-26]
mechanical/cad-2024/KickstandAssembly.SLDASM
Frame 2.0
Kickstand
KickstandBracketFeb15 x 2
