Electrium-Mobility/Bakfiets-F26/docs/images/cad-previews/steeringAssembly.png

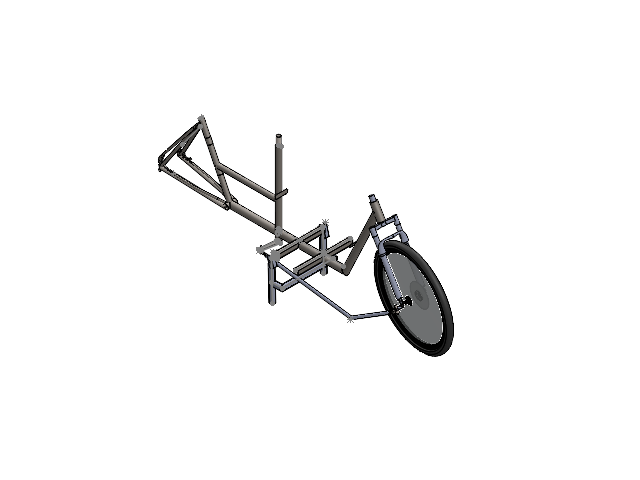
docs/images/cad-previews/steeringAssembly.png
