Electrium-Mobility/Bakfiets-F26/firmware/desk-demo/desk-demo.ino

/**************************************************************************
  Bakfiets F26 desk demo
  A ready-to-open copy of the 2024 display code (firmware/display-2024/main.cpp).
  The only change: LED_PIN moved from GPIO 9 to GPIO 5, because GPIO 9 is also
  the OLED's I2C clock (SCL). Everything else is the 2024 code, unchanged.
  Board: ESP32-S3 (Tools > Board > ESP32S3 Dev Module). See firmware/README.md.
 **************************************************************************/
/**************************************************************************
  Electrium Mobility Bakfiets display
  Contributers: Patrick He, Kimberley Hoang, Alisa Wu, Saptarshi Bhattacherya
 **************************************************************************/
#include <SPI.h>
#include <Wire.h>
#include <Adafruit_GFX.h>
#include <Adafruit_SSD1306.h>
#include <FastLED.h>

#define FASTLED_ALL_PINS_HARDWARE_SPI
#define FASTLED_ESP32_SPI_BUS HSPI
#define SCREEN_WIDTH 128
#define SCREEN_HEIGHT 64
#define SDA_PIN 10
#define SCL_PIN 9

// Declaration for an SSD1306 display connected to I2C (SDA, SCL pins)
#define OLED_RESET     -1 // Reset pin # (or -1 if sharing Arduino reset pin)
#define SCREEN_ADDRESS 0x3C ///< See datasheet for Address; 0x3D for 128x64, 0x3C for 128x32
Adafruit_SSD1306 display(SCREEN_WIDTH, SCREEN_HEIGHT, &Wire, OLED_RESET);

#define NUMFLAKES     10 // Number of snowflakes in the animation example

#define LOGO_HEIGHT   16
#define LOGO_WIDTH    16

#define LED_PIN     5   // was 9 in 2024, which clashed with SCL_PIN
#define NUM_LEDS    125

CRGB leds[NUM_LEDS];

static const unsigned char PROGMEM logo_bmp[] =
{ 0b00000000, 0b11000000,
  0b00000001, 0b11000000,
  0b00000001, 0b11000000,
  0b00000011, 0b11100000,
  0b11110011, 0b11100000,
  0b11111110, 0b11111000,
  0b01111110, 0b11111111,
  0b00110011, 0b10011111,
  0b00011111, 0b11111100,
  0b00001101, 0b01110000,
  0b00011011, 0b10100000,
  0b00111111, 0b11100000,
  0b00111111, 0b11110000,
  0b01111100, 0b11110000,
  0b01110000, 0b01110000,
  0b00000000, 0b00110000 };

void setup() {
  Serial.begin(9600);
  Wire.begin(SDA_PIN, SCL_PIN);

  // SSD1306_SWITCHCAPVCC = generate display voltage from 3.3V internally
  if(!display.begin(SSD1306_SWITCHCAPVCC, SCREEN_ADDRESS)) {
    Serial.println(F("SSD1306 allocation failed"));
    for(;;); // Don't proceed, loop forever
  }

  // Clear the buffer
  display.clearDisplay();

  FastLED.addLeds<WS2813, LED_PIN, GRB>(leds, NUM_LEDS); // Initialize FastLED
  FastLED.setBrightness(50); // Set the brightness of the LEDs (0-255)

  // Clear all LEDs to off initially
  FastLED.clear();
  FastLED.show();

  loop();
}

void drawBattery(uint8_t percentage) {
  int16_t batteryWidth = 40; 
  int16_t batteryHeight = 16;
  int16_t batteryX = SCREEN_WIDTH - batteryWidth - 80; // Position to the right
  int16_t batteryY = 8; // Position at the top

  // Calculate the width of the battery's fill
  int16_t fillWidth = (batteryWidth - 4) * percentage / 100; 

  // battery outline
  display.drawRect(batteryX, batteryY, batteryWidth, batteryHeight, SSD1306_WHITE);
  display.fillRect(batteryX + batteryWidth, batteryY + 3, 2, batteryHeight - 6, SSD1306_WHITE);

  // battery fill
  display.fillRect(batteryX + 2, batteryY + 2, fillWidth, batteryHeight - 4, SSD1306_WHITE);

  // battery percent
  display.setTextSize(2);
  display.setTextColor(SSD1306_WHITE);
  display.setCursor(batteryX + batteryWidth + 6, batteryY + 1);
  display.print(percentage);
  display.print('%');
}

// Draw speed in KM/H
void drawSpeed(uint8_t speed) {
  display.setTextSize(2);
  display.setTextColor(SSD1306_WHITE);
  display.setCursor(10, 40);
  display.println(speed);

  display.setTextSize(2);
  display.setTextColor(SSD1306_WHITE);
  display.setCursor(40, 40);
  display.println(F("KM/H"));
}

// Draw Power Assist (PA) level, e.g. 'PA 5'
void drawLevel(uint8_t level) {
  display.setTextSize(2);
  display.setTextColor(SSD1306_WHITE);
  display.setCursor(100, 10);
  display.println(F("PA"));

  display.setTextSize(2);
  display.setTextColor(SSD1306_WHITE);
  display.setCursor(105, 40);
  display.println(level);
}

// LED animation for left turn
void leftTurn() {
  for (int i = NUM_LEDS/2; i < NUM_LEDS; i++) {
    leds[i] = CRGB::Red; FastLED.show(); delay(10);
  }

  for (int i = NUM_LEDS/2; i < NUM_LEDS; i++) {
    leds[i] = CRGB::Black; FastLED.show(); delay(10);
  }
}

// LED animation for right turn
void rightTurn() {
  for (int i = NUM_LEDS/2; i >= 0; i--) {
    leds[i] = CRGB::Red; FastLED.show(); delay(10);
  }
  for (int i = NUM_LEDS/2; i >= 0; i--) {
    leds[i] = CRGB::Black; FastLED.show(); delay(10);
  }
}

void idle() {
  
}

void loop() {
  
  // test left turn signal
  rightTurn();
  rightTurn();
  rightTurn();
  rightTurn();
  rightTurn();
  


  display.clearDisplay(); 

  // Battery display
  uint8_t batteryLevel = 50;// hard coded for now but will need to figure out how to get the actual battery %
  drawBattery(batteryLevel);

  // Speed
  uint8_t speed = 36;
  drawSpeed(speed);

  // Screen divider
  display.drawLine(95, 10, 95, display.height()-11, SSD1306_WHITE);

  // PA Level
  uint8_t level = 5;
  drawLevel(level);

  display.display();



}
